Dreamy-Jy/slack/hardware/v1-electronics/Texas Instruments/BQ25186DLHR.stp

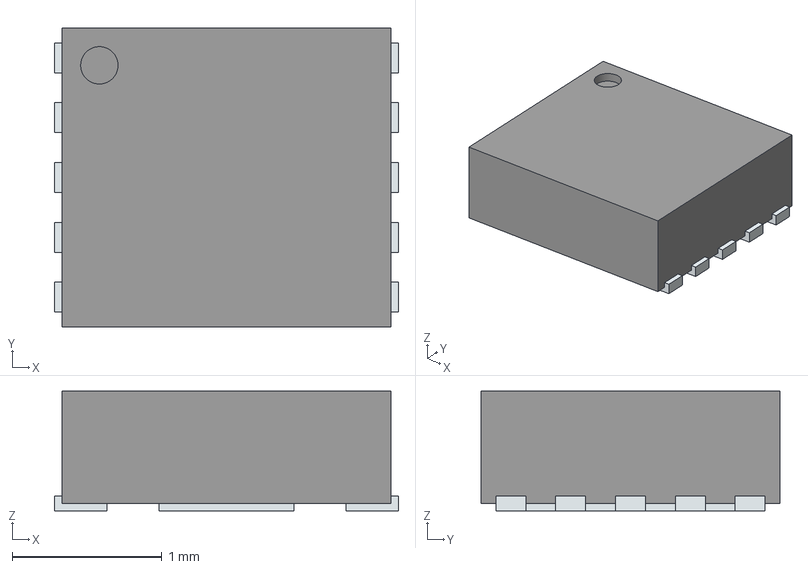
[picture p15: CAD file, 2026-05-10]
hardware/v1-electronics/Texas Instruments/BQ25186DLHR.stp
2.30 x 2.00 x 0.8 mm
ThermalPin
PinsArrayLR
