Dreamy-Jy/slack/hardware/v1-electronics/Texas Instruments/BQ25185DLHR.step

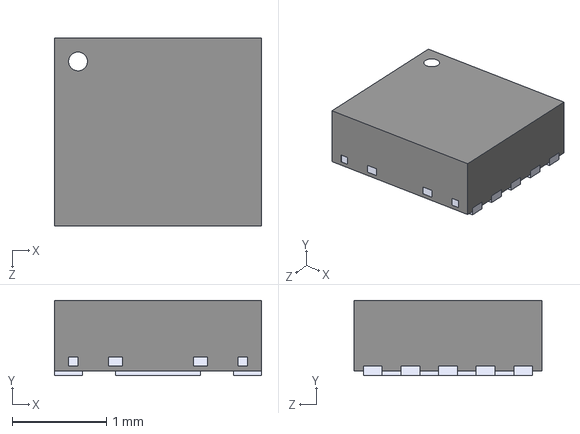
[picture p16: CAD file, 2026-04-30]
hardware/v1-electronics/Texas Instruments/BQ25185DLHR.step
2.20 x 0.8 x 2.00 mm
