Dreamy-Jy/slack/hardware/v1-electronics/controller.kicad_sch

## KiCad design hardware/v1-electronics/controller.kicad_sch (2026-08-18)

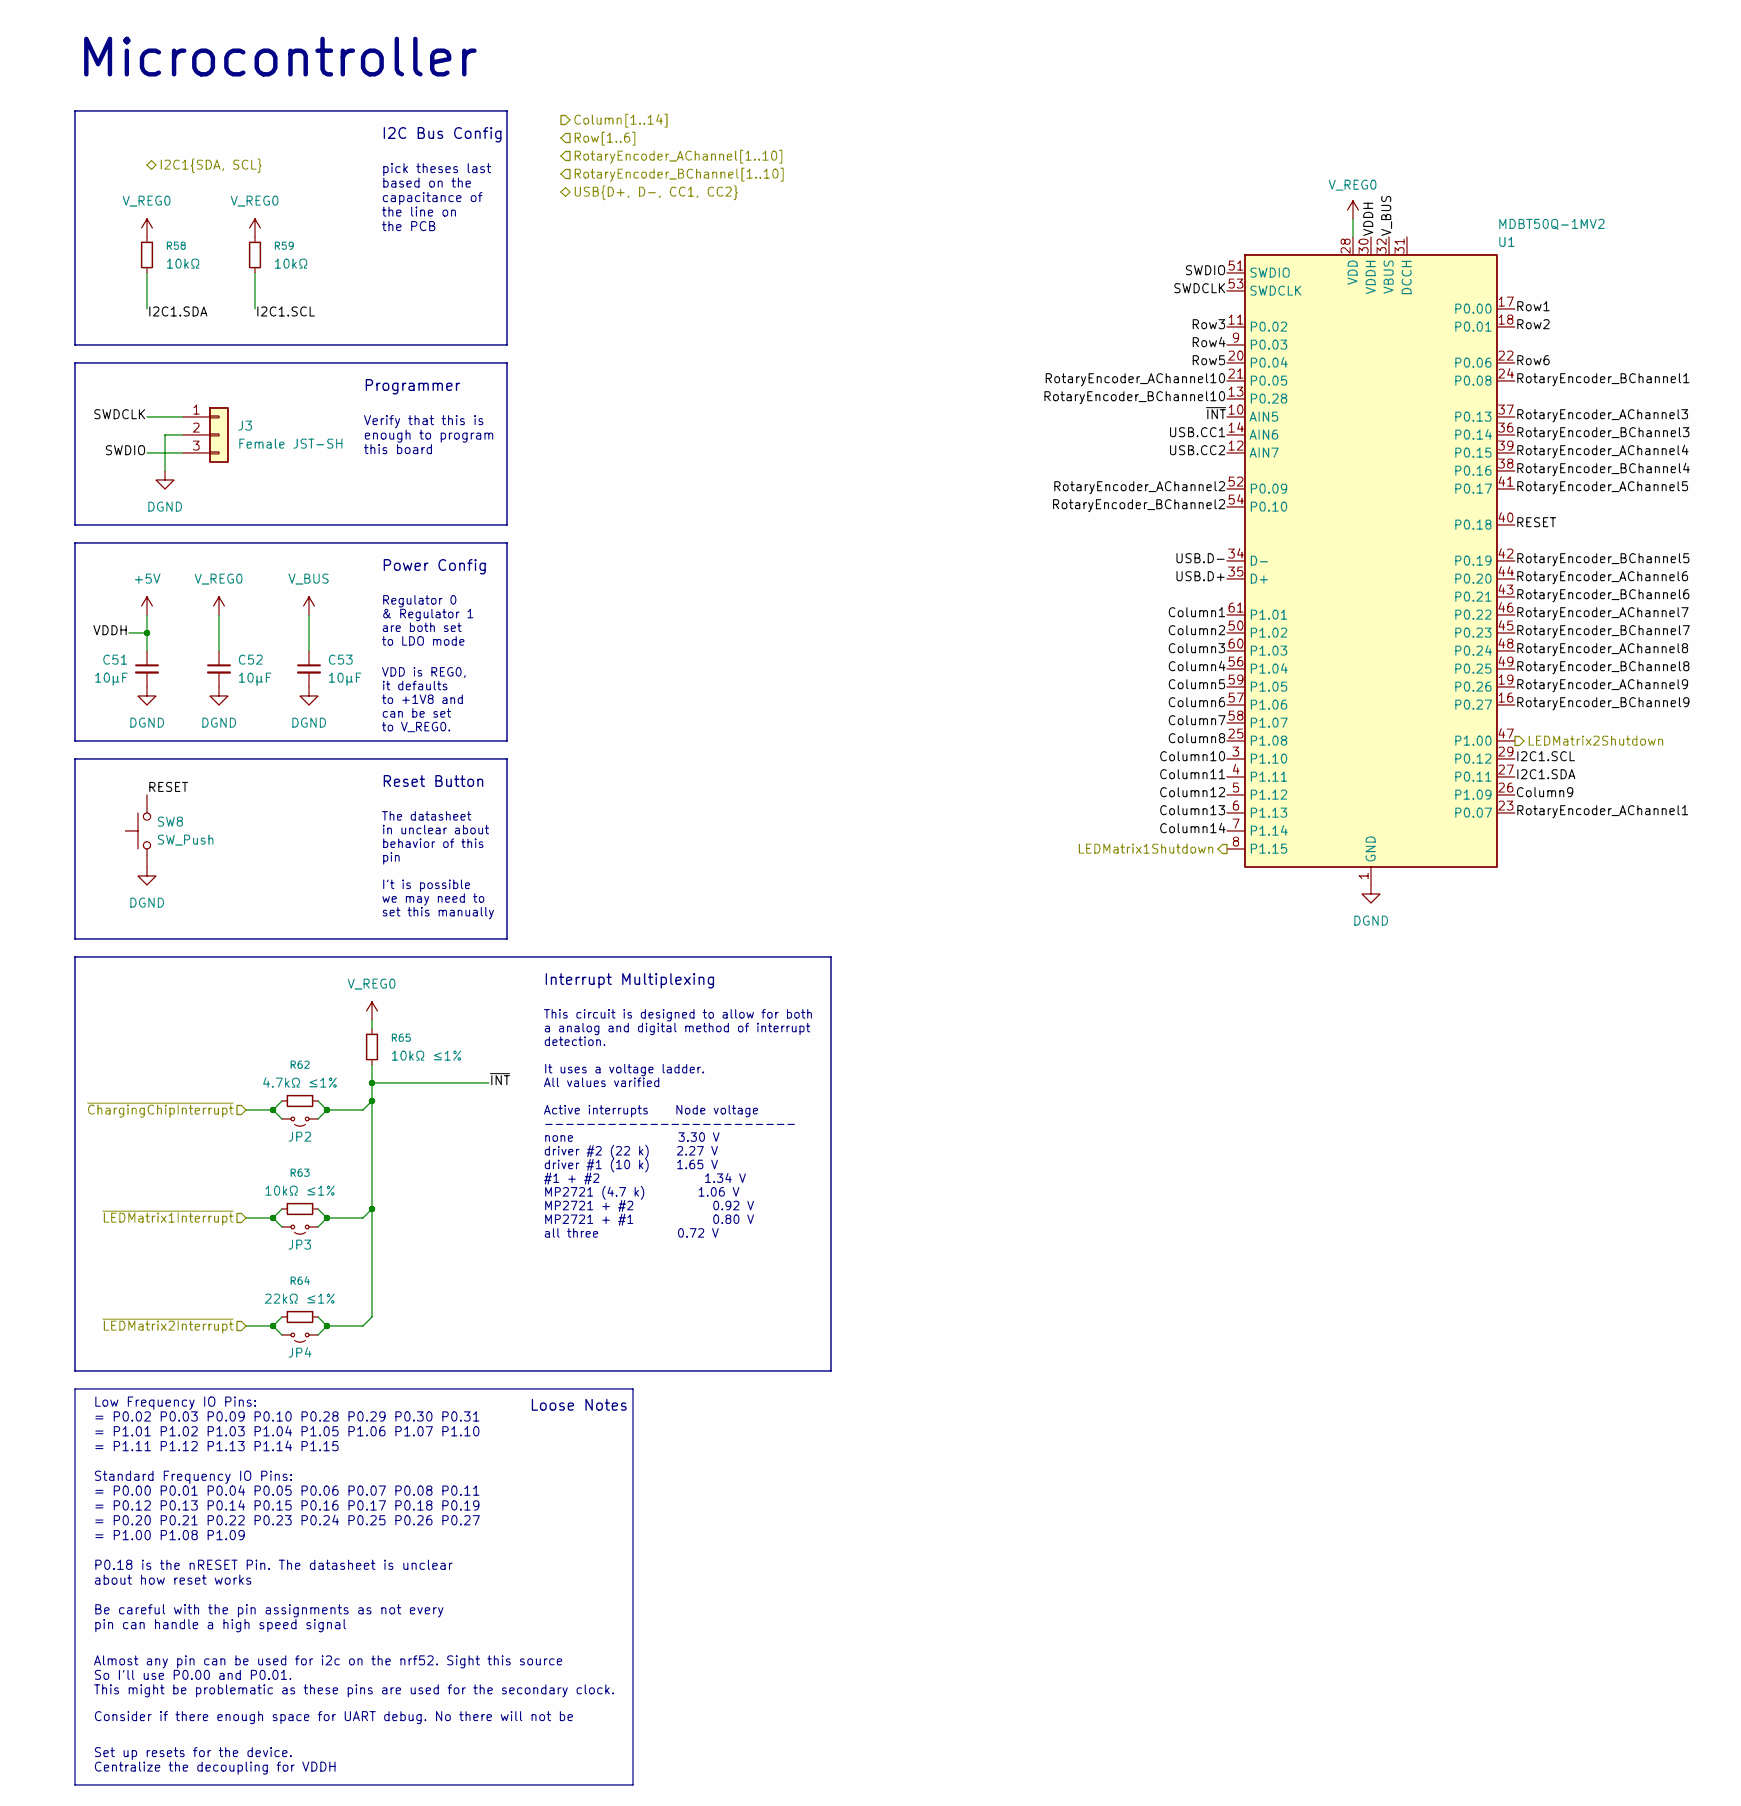
[picture p24: schematic controller.kicad_sch]

Parts:
C51, C52, C53: 10μF; C_0805_2012Metric
J3: Female JST-SH; JST_SH_BM03B-SRSS-TB_1x03-1MP_P1.00mm_Vertical
JP2, JP3, JP4: Jumper_2_Small_Open; PinHeader_1x02_P2.54mm_Vertical
R58, R59: 10kΩ; R_0805_2012Metric
R62: 4.7kΩ ≤1%; R_0805_2012Metric
R63, R65: 10kΩ ≤1%; R_0805_2012Metric
R64: 22kΩ ≤1%; R_0805_2012Metric
SW8: SW_Push; SW_Push_1P1T_XKB_TS-1187A
U1: MDBT50Q-1MV2; Raytac_MDBT50Q

Connections:
+5V: C51.1, U1.30 (VDDH)
Column1: U1.61 (P1.01)
Column2: U1.50 (P1.02)
Column3: U1.60 (P1.03)
Column4: U1.56 (P1.04)
Column5: U1.59 (P1.05)
Column6: U1.57 (P1.06)
Column7: U1.58 (P1.07)
Column8: U1.25 (P1.08)
Column9: U1.26 (P1.09)
Column10: U1.3 (P1.10)
Column11: U1.4 (P1.11)
Column12: U1.5 (P1.12)
Column13: U1.6 (P1.13)
Column14: U1.7 (P1.14)
DGND: C51.2, C52.2, C53.2, J3.2, SW8.1, U1.1 (GND), U1.2 (GND), U1.15 (GND), U1.33 (GND), U1.55 (GND)
I2C1.SCL: R59.2, U1.29 (P0.12)
I2C1.SDA: R58.2, U1.27 (P0.11)
LEDMatrix1Shutdown: U1.8 (P1.15)
LEDMatrix2Shutdown: U1.47 (P1.00)
RESET: SW8.2, U1.40 (P0.18)
RotaryEncoder_AChannel1: U1.23 (P0.07)
RotaryEncoder_AChannel2: U1.52 (P0.09)
RotaryEncoder_AChannel3: U1.37 (P0.13)
RotaryEncoder_AChannel4: U1.39 (P0.15)
RotaryEncoder_AChannel5: U1.41 (P0.17)
RotaryEncoder_AChannel6: U1.44 (P0.20)
RotaryEncoder_AChannel7: U1.46 (P0.22)
RotaryEncoder_AChannel8: U1.48 (P0.24)
RotaryEncoder_AChannel9: U1.19 (P0.26)
RotaryEncoder_AChannel10: U1.21 (P0.05)
RotaryEncoder_BChannel1: U1.24 (P0.08)
RotaryEncoder_BChannel2: U1.54 (P0.10)
RotaryEncoder_BChannel3: U1.36 (P0.14)
RotaryEncoder_BChannel4: U1.38 (P0.16)
RotaryEncoder_BChannel5: U1.42 (P0.19)
RotaryEncoder_BChannel6: U1.43 (P0.21)
RotaryEncoder_BChannel7: U1.45 (P0.23)
RotaryEncoder_BChannel8: U1.49 (P0.25)
RotaryEncoder_BChannel9: U1.16 (P0.27)
RotaryEncoder_BChannel10: U1.13 (P0.28)
Row1: U1.17 (P0.00)
Row2: U1.18 (P0.01)
Row3: U1.11 (P0.02)
Row4: U1.9 (P0.03)
Row5: U1.20 (P0.04)
Row6: U1.22 (P0.06)
SWDCLK: J3.1, U1.53 (SWDCLK)
SWDIO: J3.3, U1.51 (SWDIO)
USB.CC1: U1.14 (P0.30)
USB.CC2: U1.12 (P0.31)
USB.D+: U1.35 (D+)
USB.D-: U1.34 (D-)
V_BUS: C53.1, U1.32 (VBUS)
V_REG0: C52.1, R58.1, R59.1, R65.1, U1.28 (VDD)
~ChargingChipInterrupt: JP2.2 (B), R62.2
~INT: JP2.1 (A), JP3.1 (A), JP4.1 (A), R62.1, R63.1, R64.1, R65.2, U1.10 (P0.29)
~LEDMatrix1Interrupt: JP3.2 (B), R63.2
~LEDMatrix2Interrupt: JP4.2 (B), R64.2

Notes on the sheet:
Loose Notes
Reset Button
Microcontroller
This circuit is designed to allow for both a analog and digital method of interrupt detection. It uses a voltage ladder. All values varified Active interrupts Node voltage ------------------------ none 3.30 V driver #2 (22 k) 2.27 V driver #1 (10 k) 1.65 V #1 + #2 1.34 V MP2721 (4.7 k) 1.06 V MP272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
The datasheet in unclear about behavior of this pin I't is possible we may need to set this manually
Power Config
Interrupt Multiplexing
pick theses last based on the capacitance of the line on the PCB
Low Frequency IO Pins: = P0.02 P0.03 P0.09 P0.10 P0.28 P0.29 P0.30 P0.31 = P1.01 P1.02 P1.03 P1.04 P1.05 P1.06 P1.07 P1.10 = P1.11 P1.12 P1.13 P1.14 P1.15 Standard Frequency IO Pins: = P0.00 P0.01 P0.04 P0.05 P0.06 P0.07 P0.08 P0.11 = P0.12 P0.13 P0.14 P0.15 P0.16 P0.17 P0.18 P0.19 = P0.20 P0.21 P0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
I2C Bus Config
VDD is REG0, it defaults to +1V8 and can be set to V_REG0.
Set up resets for the device. Centralize the decoupling for VDDH
Consider if there enough space for UART debug. No there will not be
Verify that this is enough to program this board
Almost any pin can be used for i2c on the nrf52. Sight this source So I'll use P0.00 and P0.01. This might be problematic as these pins are used for the secondary clock.
Regulator 0 & Regulator 1 are both set to LDO mode
Programmer
