Dreamy-Jy/slack/hardware/v1-electronics/led_matrix.kicad_sch

## KiCad design hardware/v1-electronics/led_matrix.kicad_sch (2026-08-18)

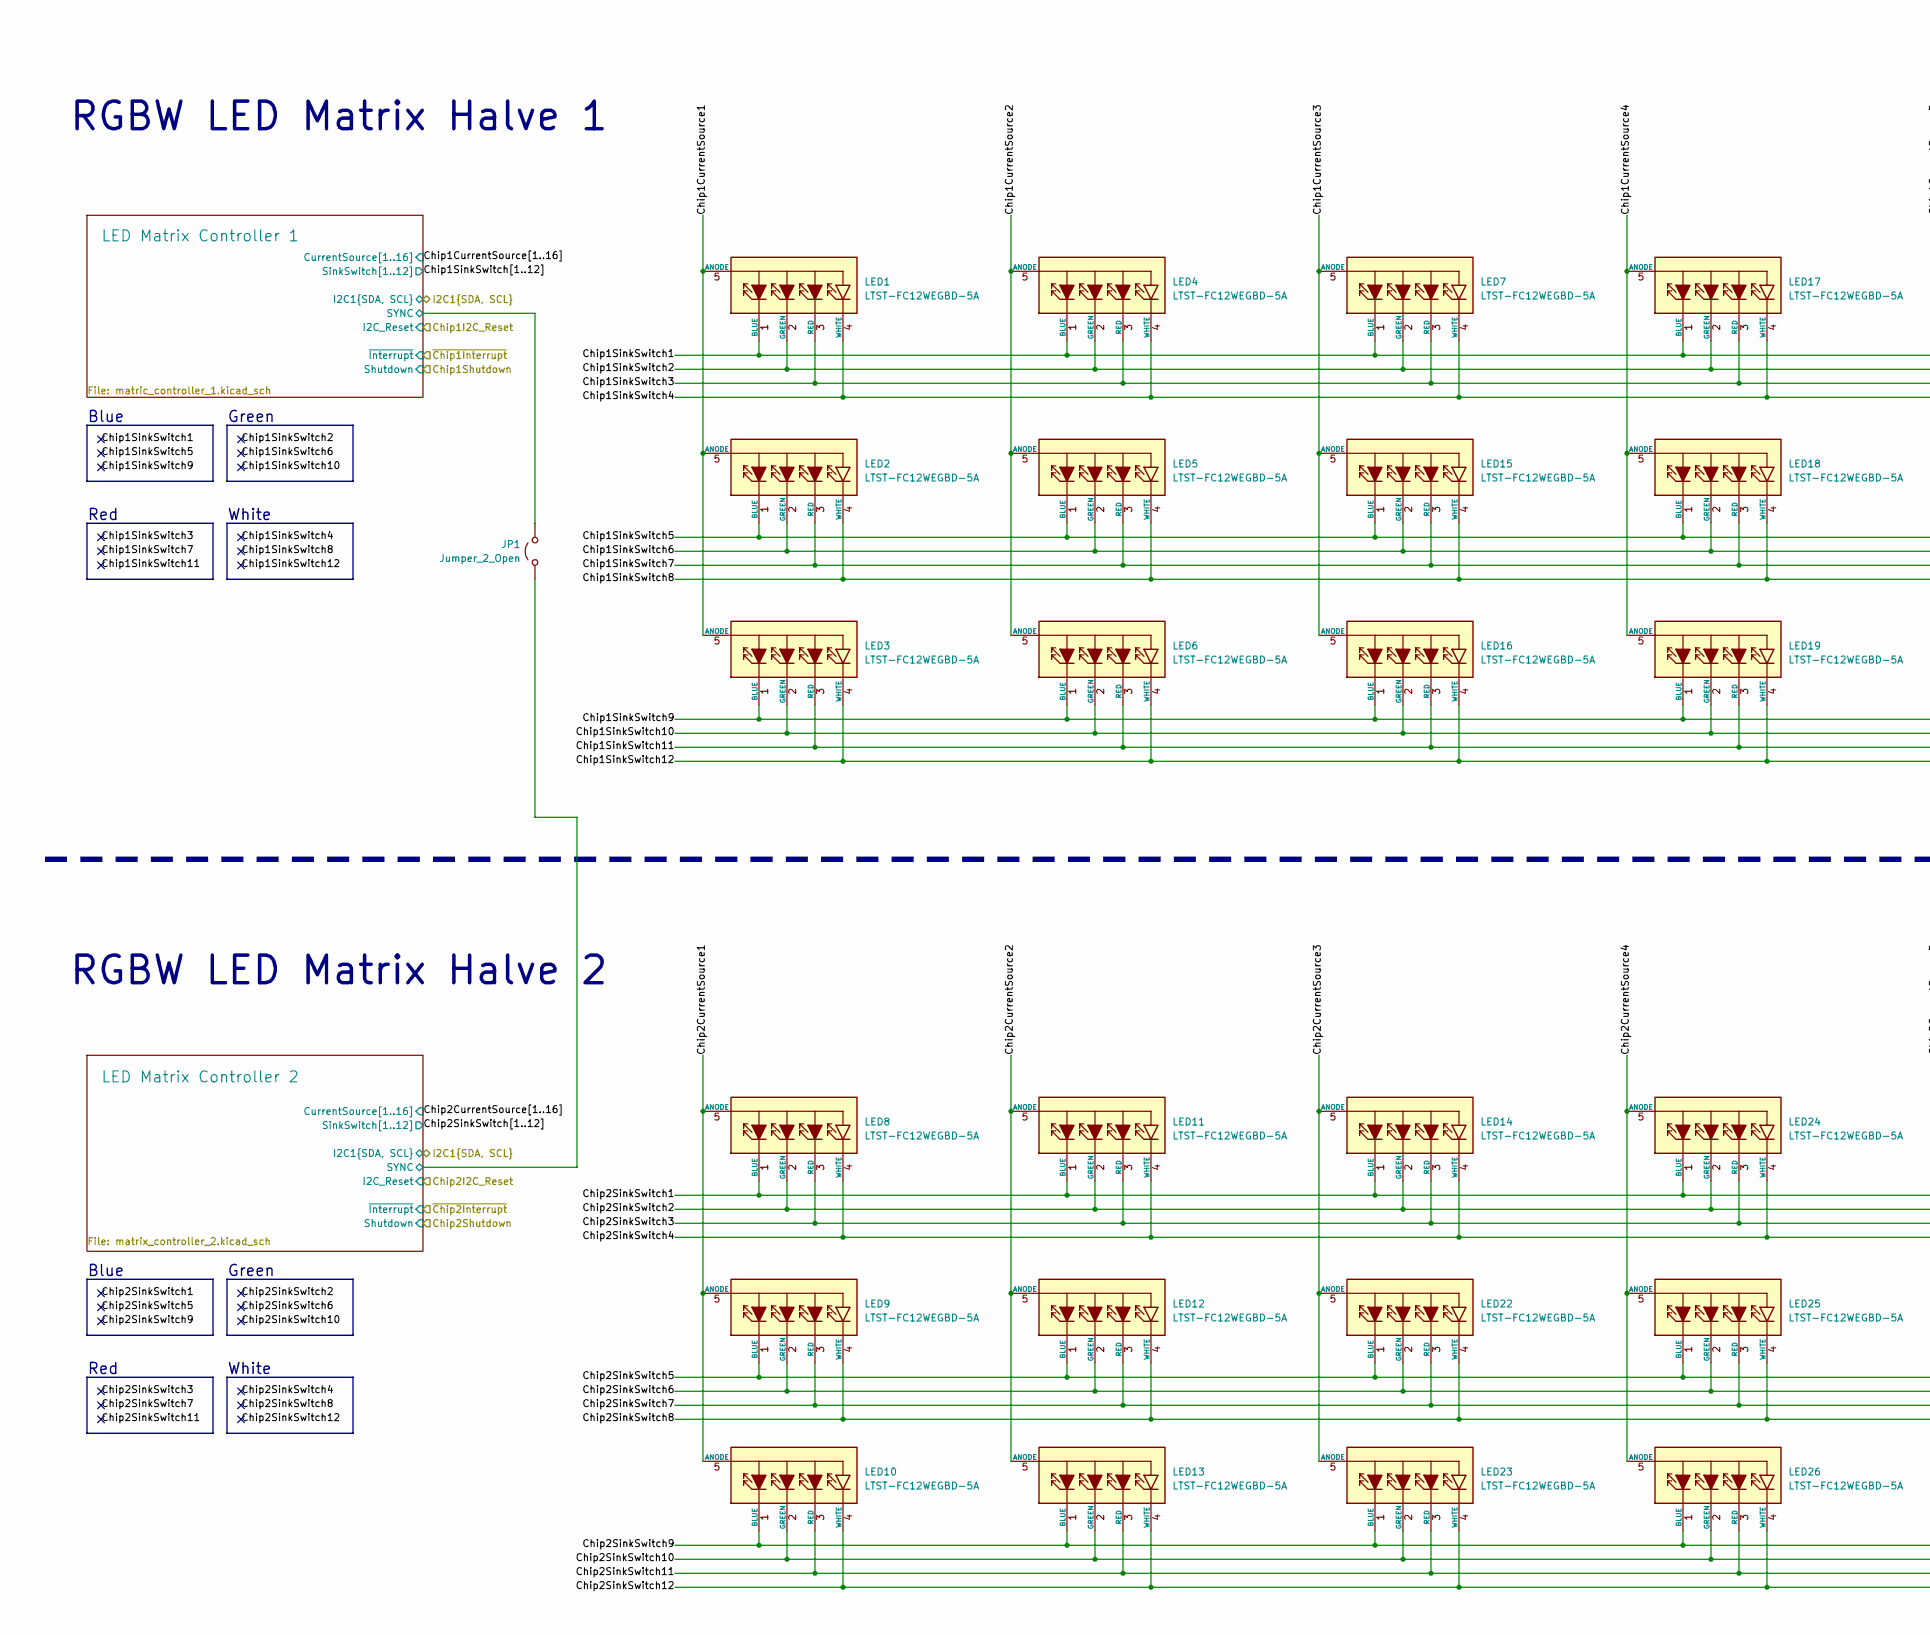
[picture p25: schematic led_matrix.kicad_sch, part in row 1, column 1]

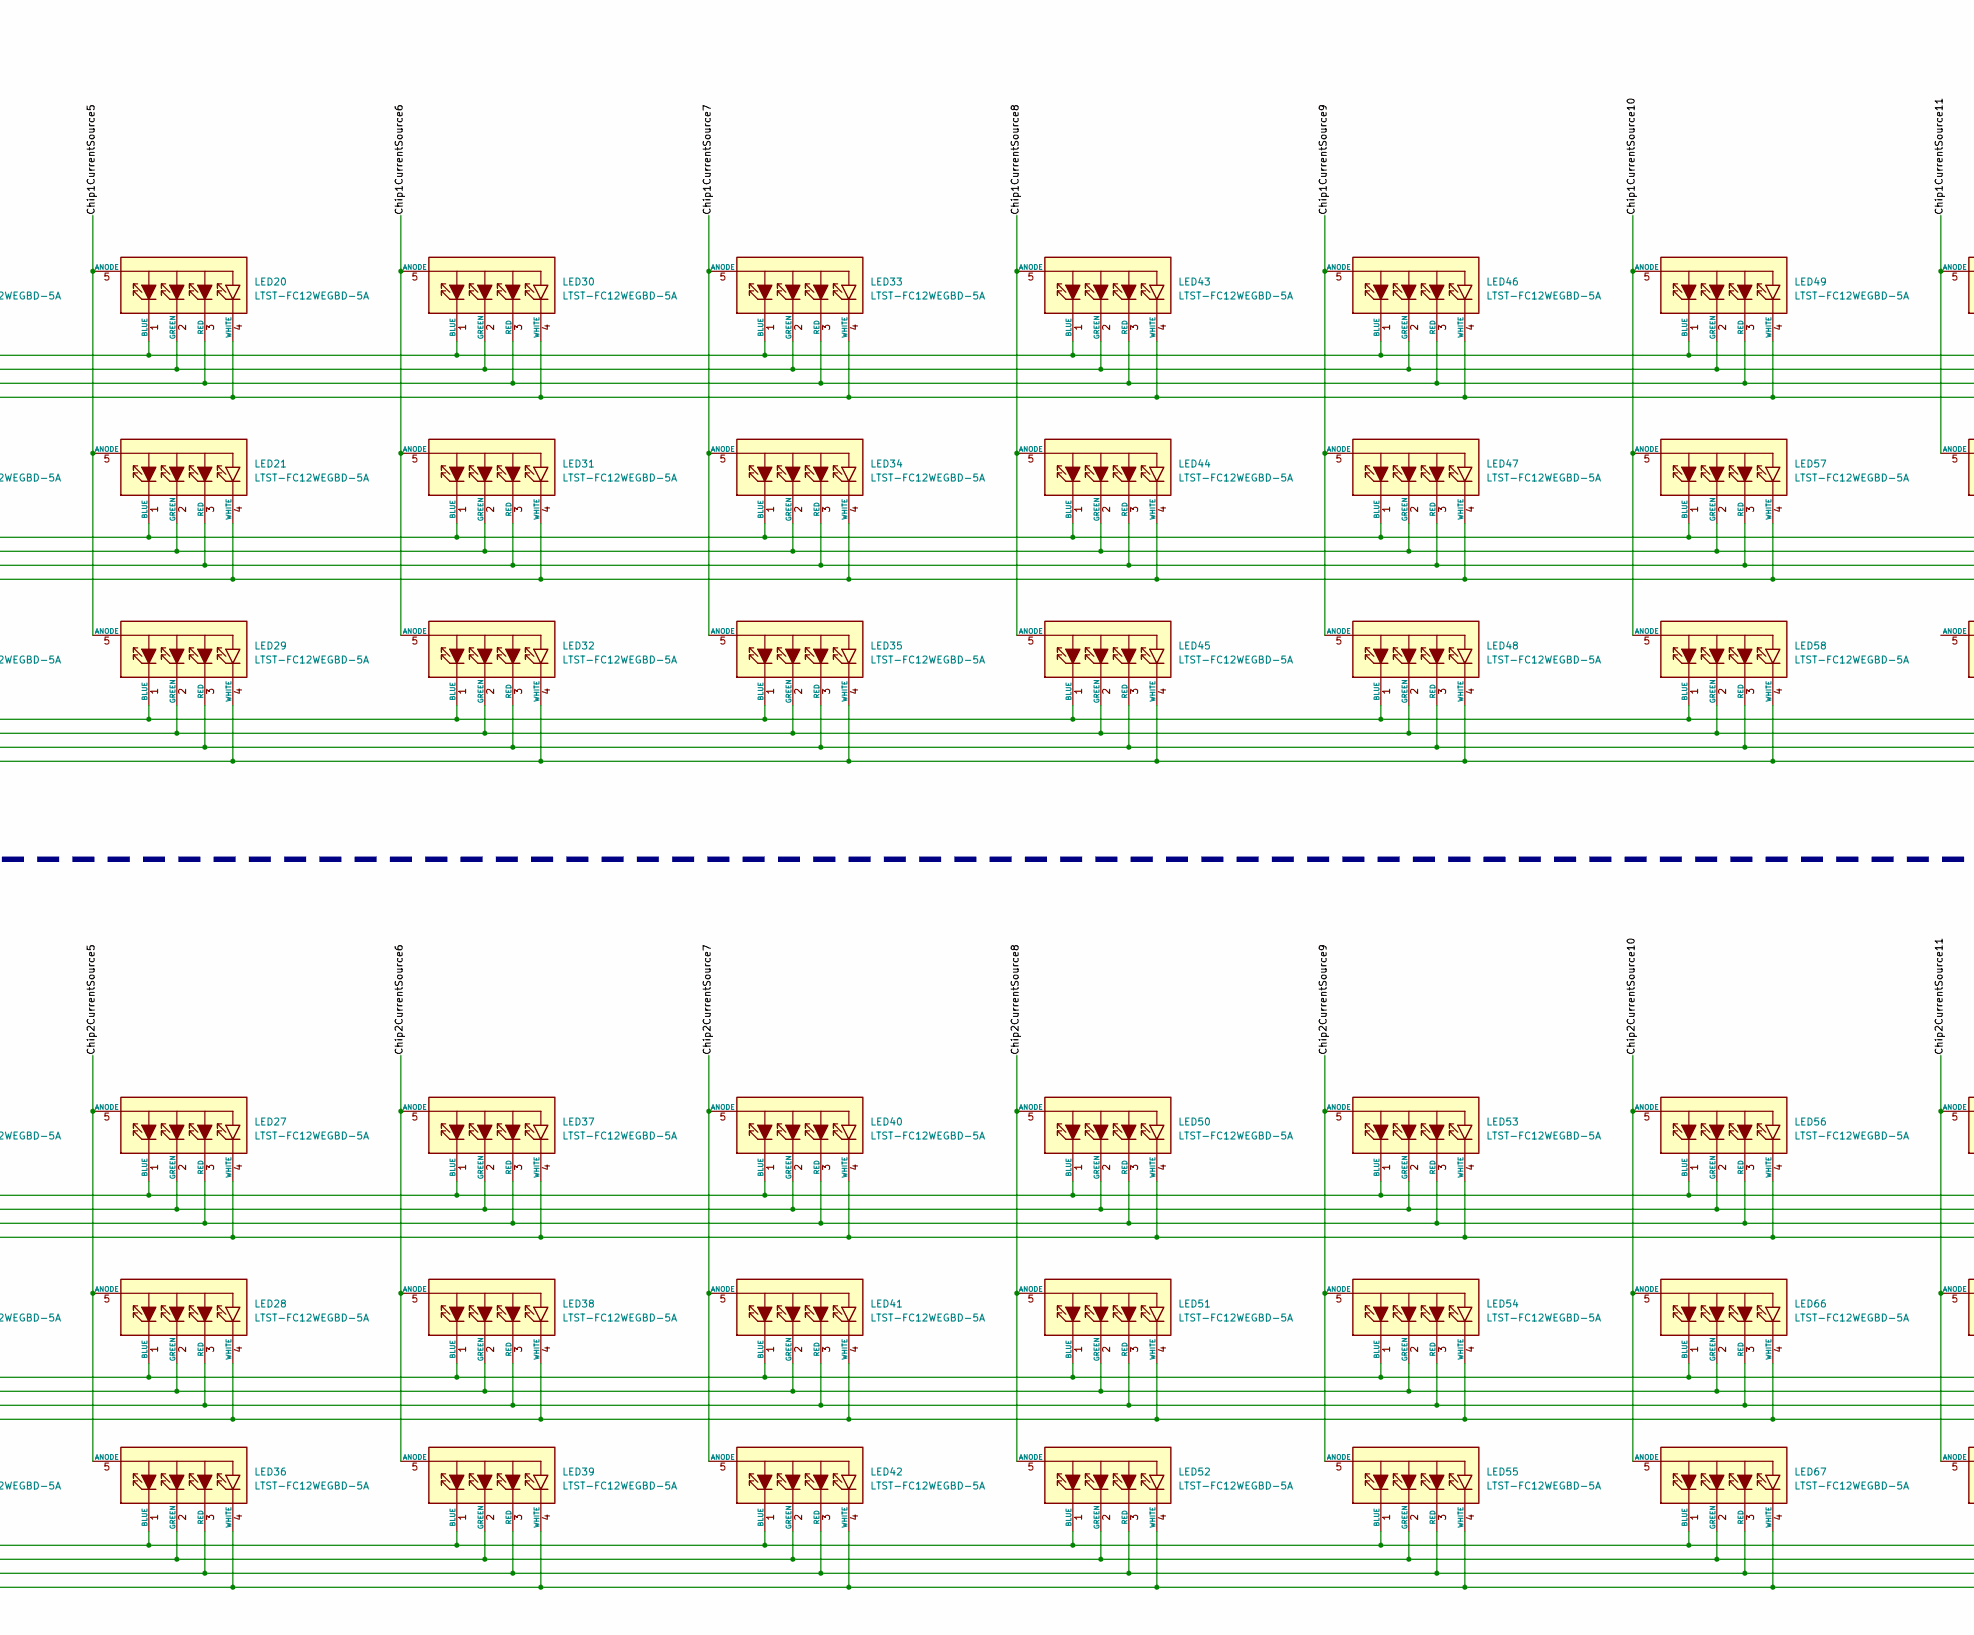
[picture p26: schematic led_matrix.kicad_sch, part in row 1, column 2]

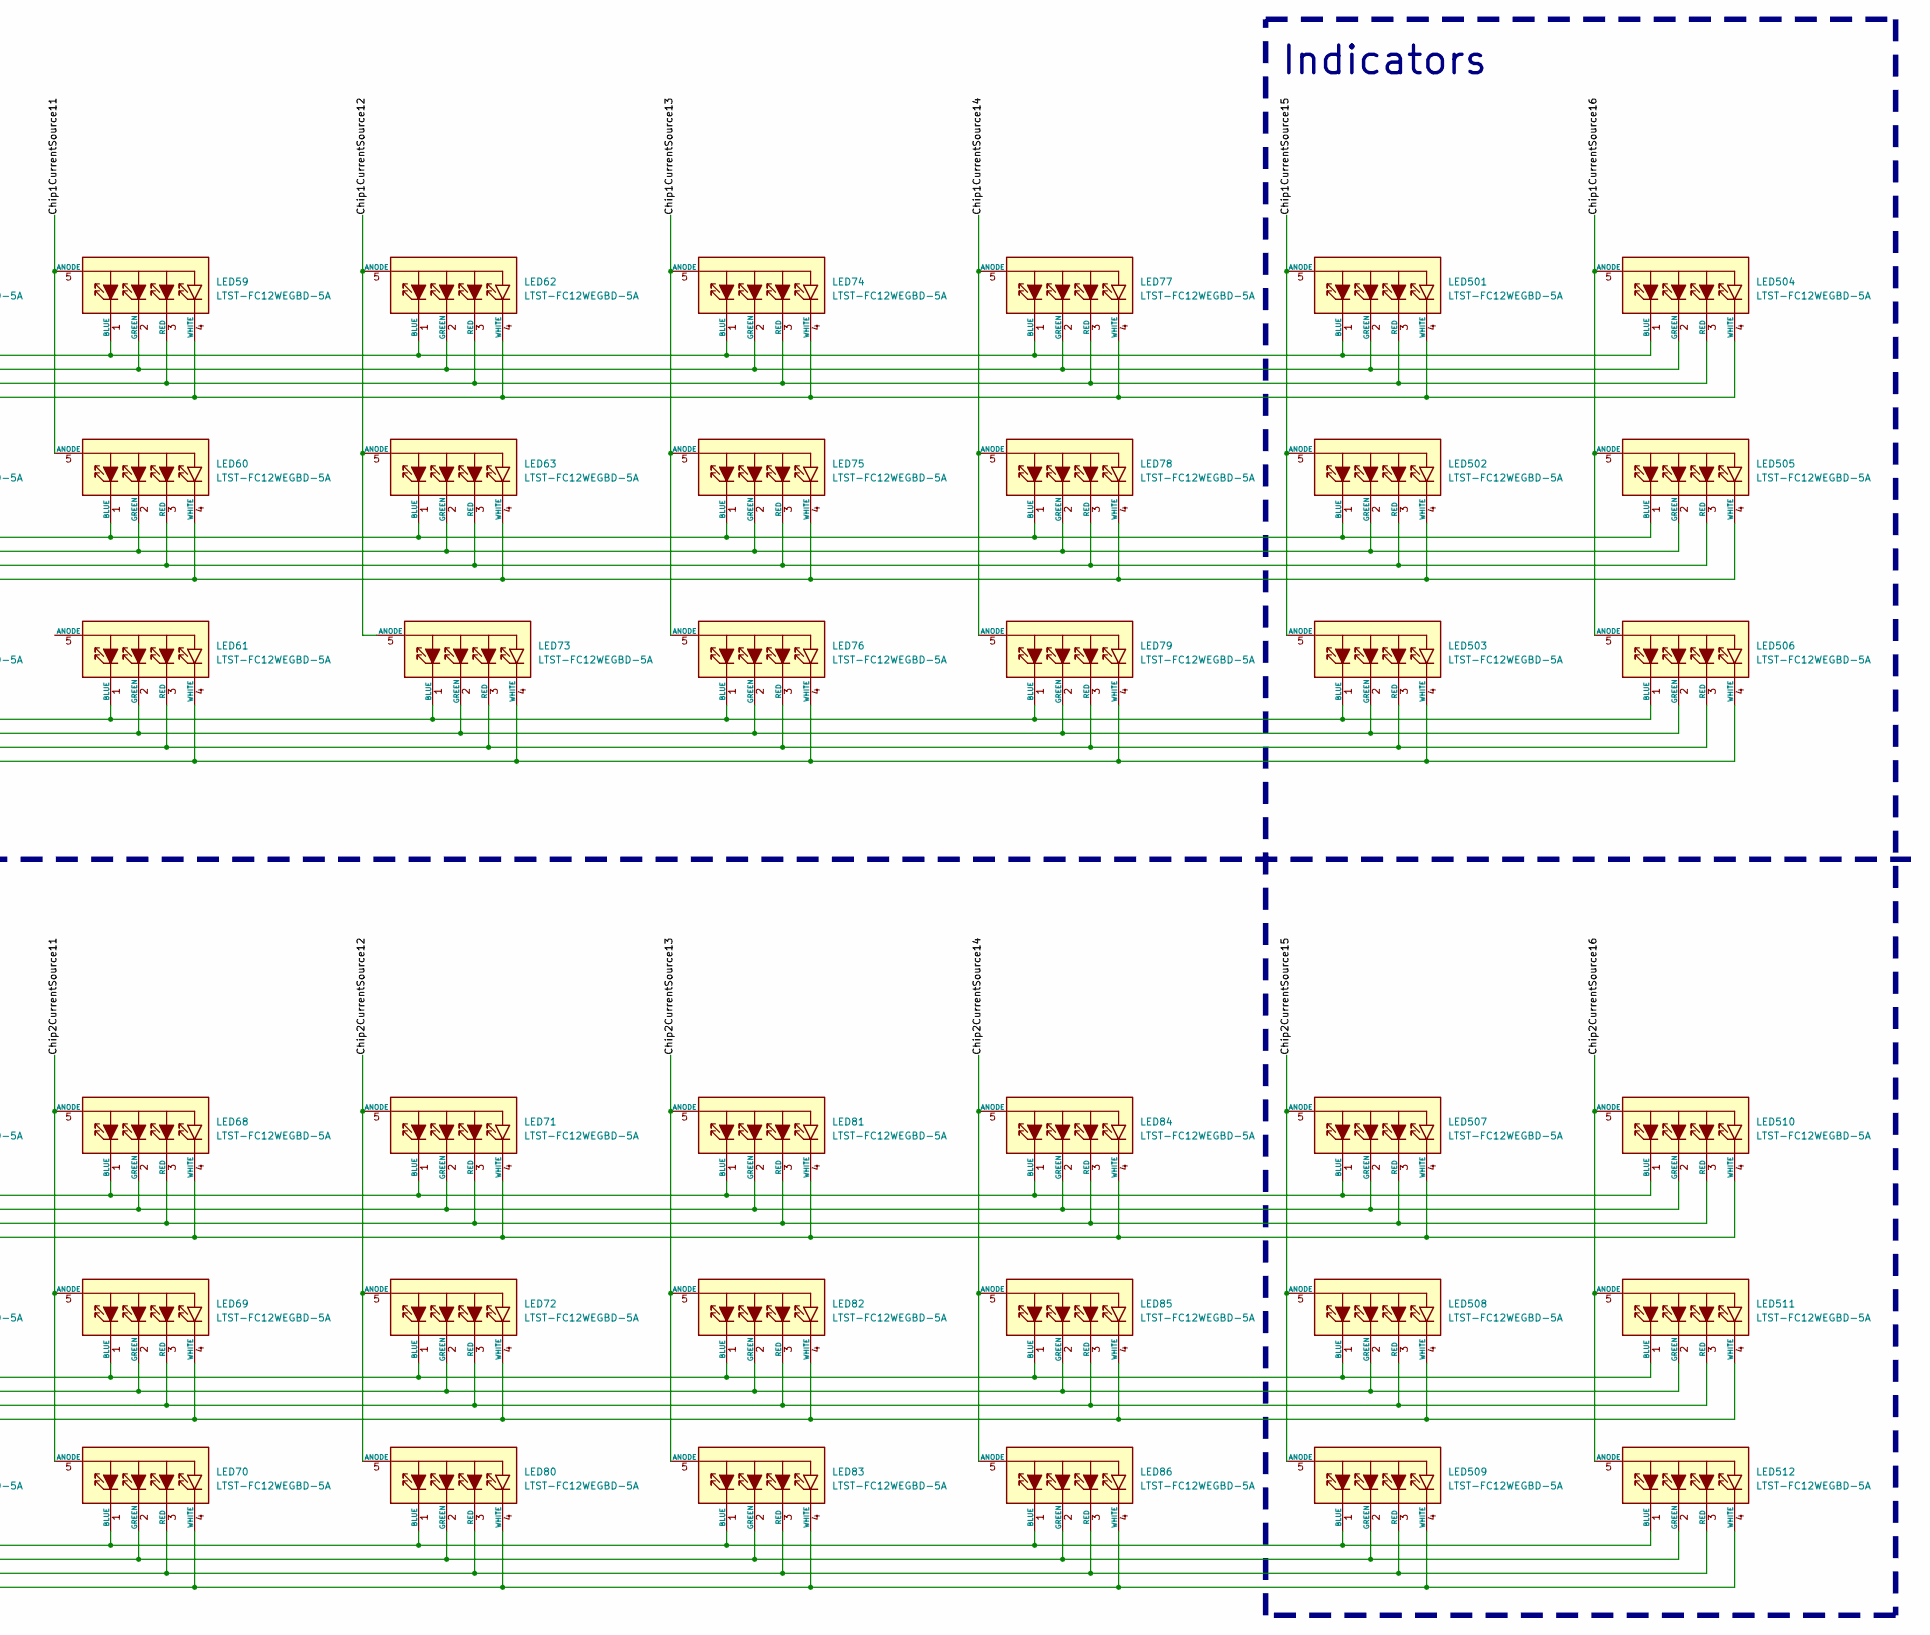
[picture p27: schematic led_matrix.kicad_sch, part in row 1, column 3]

Parts:
JP1: Jumper_2_Open; PinHeader_1x02_P2.54mm_Vertical
LED1, LED2, LED3, LED4, LED5, LED6, LED7, LED8, LED9, LED10, LED11, LED12, LED13, LED14, LED15, LED16, LED17, LED18, LED19, LED20, LED21, LED22, LED23, LED24, LED25, LED26, LED27, LED28, LED29, LED30, LED31, LED32, LED33, LED34, LED35, LED36, LED37, LED38, LED39, LED40, LED41, LED42, LED43, LED44, LED45, LED46, LED47, LED48, LED49, LED50, LED51, LED52, LED53, LED54, LED55, LED56, LED57, LED58, LED59, LED60, LED61, LED62, LED63, LED66, LED67, LED68, LED69, LED70, LED71, LED72, LED73, LED74, LED75, LED76, LED77, LED78, LED79, LED80, LED81, LED82, LED83, LED84, LED85, LED86, LED501, LED502, LED503, LED504, LED505, LED506, LED507, LED508, LED509, LED510, LED511, LED512: LTST-FC12WEGBD-5A; LTSTFC12WEGBD5A; Manufacturer_Part_Number LTST-FC12WEGBD-5A; Mouser Part Number 859-LTST-FC12WEGBD5A

Connections:
Chip1CurrentSource1: LED1.5 (ANODE), LED2.5 (ANODE), LED3.5 (ANODE)
Chip1CurrentSource2: LED4.5 (ANODE), LED5.5 (ANODE), LED6.5 (ANODE)
Chip1CurrentSource3: LED7.5 (ANODE), LED15.5 (ANODE), LED16.5 (ANODE)
Chip1CurrentSource4: LED17.5 (ANODE), LED18.5 (ANODE), LED19.5 (ANODE)
Chip1CurrentSource5: LED20.5 (ANODE), LED21.5 (ANODE), LED29.5 (ANODE)
Chip1CurrentSource6: LED30.5 (ANODE), LED31.5 (ANODE), LED32.5 (ANODE)
Chip1CurrentSource7: LED33.5 (ANODE), LED34.5 (ANODE), LED35.5 (ANODE)
Chip1CurrentSource8: LED43.5 (ANODE), LED44.5 (ANODE), LED45.5 (ANODE)
Chip1CurrentSource9: LED46.5 (ANODE), LED47.5 (ANODE), LED48.5 (ANODE)
Chip1CurrentSource10: LED49.5 (ANODE), LED57.5 (ANODE), LED58.5 (ANODE)
Chip1CurrentSource11: LED59.5 (ANODE), LED60.5 (ANODE)
Chip1CurrentSource12: LED62.5 (ANODE), LED63.5 (ANODE), LED73.5 (ANODE)
Chip1CurrentSource13: LED74.5 (ANODE), LED75.5 (ANODE), LED76.5 (ANODE)
Chip1CurrentSource14: LED77.5 (ANODE), LED78.5 (ANODE), LED79.5 (ANODE)
Chip1CurrentSource15: LED501.5 (ANODE), LED502.5 (ANODE), LED503.5 (ANODE)
Chip1CurrentSource16: LED504.5 (ANODE), LED505.5 (ANODE), LED506.5 (ANODE)
Chip1SinkSwitch1: LED1.1 (BLUE), LED4.1 (BLUE), LED7.1 (BLUE), LED17.1 (BLUE), LED20.1 (BLUE), LED30.1 (BLUE), LED33.1 (BLUE), LED43.1 (BLUE), LED46.1 (BLUE), LED49.1 (BLUE), LED59.1 (BLUE), LED62.1 (BLUE), LED74.1 (BLUE), LED77.1 (BLUE), LED501.1 (BLUE), LED504.1 (BLUE)
Chip1SinkSwitch2: LED1.2 (GREEN), LED4.2 (GREEN), LED7.2 (GREEN), LED17.2 (GREEN), LED20.2 (GREEN), LED30.2 (GREEN), LED33.2 (GREEN), LED43.2 (GREEN), LED46.2 (GREEN), LED49.2 (GREEN), LED59.2 (GREEN), LED62.2 (GREEN), LED74.2 (GREEN), LED77.2 (GREEN), LED501.2 (GREEN), LED504.2 (GREEN)
Chip1SinkSwitch3: LED1.3 (RED), LED4.3 (RED), LED7.3 (RED), LED17.3 (RED), LED20.3 (RED), LED30.3 (RED), LED33.3 (RED), LED43.3 (RED), LED46.3 (RED), LED49.3 (RED), LED59.3 (RED), LED62.3 (RED), LED74.3 (RED), LED77.3 (RED), LED501.3 (RED), LED504.3 (RED)
Chip1SinkSwitch4: LED1.4 (WHITE), LED4.4 (WHITE), LED7.4 (WHITE), LED17.4 (WHITE), LED20.4 (WHITE), LED30.4 (WHITE), LED33.4 (WHITE), LED43.4 (WHITE), LED46.4 (WHITE), LED49.4 (WHITE), LED59.4 (WHITE), LED62.4 (WHITE), LED74.4 (WHITE), LED77.4 (WHITE), LED501.4 (WHITE), LED504.4 (WHITE)
Chip1SinkSwitch5: LED2.1 (BLUE), LED5.1 (BLUE), LED15.1 (BLUE), LED18.1 (BLUE), LED21.1 (BLUE), LED31.1 (BLUE), LED34.1 (BLUE), LED44.1 (BLUE), LED47.1 (BLUE), LED57.1 (BLUE), LED60.1 (BLUE), LED63.1 (BLUE), LED75.1 (BLUE), LED78.1 (BLUE), LED502.1 (BLUE), LED505.1 (BLUE)
Chip1SinkSwitch6: LED2.2 (GREEN), LED5.2 (GREEN), LED15.2 (GREEN), LED18.2 (GREEN), LED21.2 (GREEN), LED31.2 (GREEN), LED34.2 (GREEN), LED44.2 (GREEN), LED47.2 (GREEN), LED57.2 (GREEN), LED60.2 (GREEN), LED63.2 (GREEN), LED75.2 (GREEN), LED78.2 (GREEN), LED502.2 (GREEN), LED505.2 (GREEN)
Chip1SinkSwitch7: LED2.3 (RED), LED5.3 (RED), LED15.3 (RED), LED18.3 (RED), LED21.3 (RED), LED31.3 (RED), LED34.3 (RED), LED44.3 (RED), LED47.3 (RED), LED57.3 (RED), LED60.3 (RED), LED63.3 (RED), LED75.3 (RED), LED78.3 (RED), LED502.3 (RED), LED505.3 (RED)
Chip1SinkSwitch8: LED2.4 (WHITE), LED5.4 (WHITE), LED15.4 (WHITE), LED18.4 (WHITE), LED21.4 (WHITE), LED31.4 (WHITE), LED34.4 (WHITE), LED44.4 (WHITE), LED47.4 (WHITE), LED57.4 (WHITE), LED60.4 (WHITE), LED63.4 (WHITE), LED75.4 (WHITE), LED78.4 (WHITE), LED502.4 (WHITE), LED505.4 (WHITE)
Chip1SinkSwitch9: LED3.1 (BLUE), LED6.1 (BLUE), LED16.1 (BLUE), LED19.1 (BLUE), LED29.1 (BLUE), LED32.1 (BLUE), LED35.1 (BLUE), LED45.1 (BLUE), LED48.1 (BLUE), LED58.1 (BLUE), LED61.1 (BLUE), LED73.1 (BLUE), LED76.1 (BLUE), LED79.1 (BLUE), LED503.1 (BLUE), LED506.1 (BLUE)
Chip1SinkSwitch10: LED3.2 (GREEN), LED6.2 (GREEN), LED16.2 (GREEN), LED19.2 (GREEN), LED29.2 (GREEN), LED32.2 (GREEN), LED35.2 (GREEN), LED45.2 (GREEN), LED48.2 (GREEN), LED58.2 (GREEN), LED61.2 (GREEN), LED73.2 (GREEN), LED76.2 (GREEN), LED79.2 (GREEN), LED503.2 (GREEN), LED506.2 (GREEN)
Chip1SinkSwitch11: LED3.3 (RED), LED6.3 (RED), LED16.3 (RED), LED19.3 (RED), LED29.3 (RED), LED32.3 (RED), LED35.3 (RED), LED45.3 (RED), LED48.3 (RED), LED58.3 (RED), LED61.3 (RED), LED73.3 (RED), LED76.3 (RED), LED79.3 (RED), LED503.3 (RED), LED506.3 (RED)
Chip1SinkSwitch12: LED3.4 (WHITE), LED6.4 (WHITE), LED16.4 (WHITE), LED19.4 (WHITE), LED29.4 (WHITE), LED32.4 (WHITE), LED35.4 (WHITE), LED45.4 (WHITE), LED48.4 (WHITE), LED58.4 (WHITE), LED61.4 (WHITE), LED73.4 (WHITE), LED76.4 (WHITE), LED79.4 (WHITE), LED503.4 (WHITE), LED506.4 (WHITE)
Chip2CurrentSource1: LED8.5 (ANODE), LED9.5 (ANODE), LED10.5 (ANODE)
Chip2CurrentSource2: LED11.5 (ANODE), LED12.5 (ANODE), LED13.5 (ANODE)
Chip2CurrentSource3: LED14.5 (ANODE), LED22.5 (ANODE), LED23.5 (ANODE)
Chip2CurrentSource4: LED24.5 (ANODE), LED25.5 (ANODE), LED26.5 (ANODE)
Chip2CurrentSource5: LED27.5 (ANODE), LED28.5 (ANODE), LED36.5 (ANODE)
Chip2CurrentSource6: LED37.5 (ANODE), LED38.5 (ANODE), LED39.5 (ANODE)
Chip2CurrentSource7: LED40.5 (ANODE), LED41.5 (ANODE), LED42.5 (ANODE)
Chip2CurrentSource8: LED50.5 (ANODE), LED51.5 (ANODE), LED52.5 (ANODE)
Chip2CurrentSource9: LED53.5 (ANODE), LED54.5 (ANODE), LED55.5 (ANODE)
Chip2CurrentSource10: LED56.5 (ANODE), LED66.5 (ANODE), LED67.5 (ANODE)
Chip2CurrentSource11: LED68.5 (ANODE), LED69.5 (ANODE), LED70.5 (ANODE)
Chip2CurrentSource12: LED71.5 (ANODE), LED72.5 (ANODE), LED80.5 (ANODE)
Chip2CurrentSource13: LED81.5 (ANODE), LED82.5 (ANODE), LED83.5 (ANODE)
Chip2CurrentSource14: LED84.5 (ANODE), LED85.5 (ANODE), LED86.5 (ANODE)
Chip2CurrentSource15: LED507.5 (ANODE), LED508.5 (ANODE), LED509.5 (ANODE)
Chip2CurrentSource16: LED510.5 (ANODE), LED511.5 (ANODE), LED512.5 (ANODE)
Chip2SinkSwitch1: LED8.1 (BLUE), LED11.1 (BLUE), LED14.1 (BLUE), LED24.1 (BLUE), LED27.1 (BLUE), LED37.1 (BLUE), LED40.1 (BLUE), LED50.1 (BLUE), LED53.1 (BLUE), LED56.1 (BLUE), LED68.1 (BLUE), LED71.1 (BLUE), LED81.1 (BLUE), LED84.1 (BLUE), LED507.1 (BLUE), LED510.1 (BLUE)
Chip2SinkSwitch2: LED8.2 (GREEN), LED11.2 (GREEN), LED14.2 (GREEN), LED24.2 (GREEN), LED27.2 (GREEN), LED37.2 (GREEN), LED40.2 (GREEN), LED50.2 (GREEN), LED53.2 (GREEN), LED56.2 (GREEN), LED68.2 (GREEN), LED71.2 (GREEN), LED81.2 (GREEN), LED84.2 (GREEN), LED507.2 (GREEN), LED510.2 (GREEN)
Chip2SinkSwitch3: LED8.3 (RED), LED11.3 (RED), LED14.3 (RED), LED24.3 (RED), LED27.3 (RED), LED37.3 (RED), LED40.3 (RED), LED50.3 (RED), LED53.3 (RED), LED56.3 (RED), LED68.3 (RED), LED71.3 (RED), LED81.3 (RED), LED84.3 (RED), LED507.3 (RED), LED510.3 (RED)
Chip2SinkSwitch4: LED8.4 (WHITE), LED11.4 (WHITE), LED14.4 (WHITE), LED24.4 (WHITE), LED27.4 (WHITE), LED37.4 (WHITE), LED40.4 (WHITE), LED50.4 (WHITE), LED53.4 (WHITE), LED56.4 (WHITE), LED68.4 (WHITE), LED71.4 (WHITE), LED81.4 (WHITE), LED84.4 (WHITE), LED507.4 (WHITE), LED510.4 (WHITE)
Chip2SinkSwitch5: LED9.1 (BLUE), LED12.1 (BLUE), LED22.1 (BLUE), LED25.1 (BLUE), LED28.1 (BLUE), LED38.1 (BLUE), LED41.1 (BLUE), LED51.1 (BLUE), LED54.1 (BLUE), LED66.1 (BLUE), LED69.1 (BLUE), LED72.1 (BLUE), LED82.1 (BLUE), LED85.1 (BLUE), LED508.1 (BLUE), LED511.1 (BLUE)
Chip2SinkSwitch6: LED9.2 (GREEN), LED12.2 (GREEN), LED22.2 (GREEN), LED25.2 (GREEN), LED28.2 (GREEN), LED38.2 (GREEN), LED41.2 (GREEN), LED51.2 (GREEN), LED54.2 (GREEN), LED66.2 (GREEN), LED69.2 (GREEN), LED72.2 (GREEN), LED82.2 (GREEN), LED85.2 (GREEN), LED508.2 (GREEN), LED511.2 (GREEN)
Chip2SinkSwitch7: LED9.3 (RED), LED12.3 (RED), LED22.3 (RED), LED25.3 (RED), LED28.3 (RED), LED38.3 (RED), LED41.3 (RED), LED51.3 (RED), LED54.3 (RED), LED66.3 (RED), LED69.3 (RED), LED72.3 (RED), LED82.3 (RED), LED85.3 (RED), LED508.3 (RED), LED511.3 (RED)
Chip2SinkSwitch8: LED9.4 (WHITE), LED12.4 (WHITE), LED22.4 (WHITE), LED25.4 (WHITE), LED28.4 (WHITE), LED38.4 (WHITE), LED41.4 (WHITE), LED51.4 (WHITE), LED54.4 (WHITE), LED66.4 (WHITE), LED69.4 (WHITE), LED72.4 (WHITE), LED82.4 (WHITE), LED85.4 (WHITE), LED508.4 (WHITE), LED511.4 (WHITE)
Chip2SinkSwitch9: LED10.1 (BLUE), LED13.1 (BLUE), LED23.1 (BLUE), LED26.1 (BLUE), LED36.1 (BLUE), LED39.1 (BLUE), LED42.1 (BLUE), LED52.1 (BLUE), LED55.1 (BLUE), LED67.1 (BLUE), LED70.1 (BLUE), LED80.1 (BLUE), LED83.1 (BLUE), LED86.1 (BLUE), LED509.1 (BLUE), LED512.1 (BLUE)
Chip2SinkSwitch10: LED10.2 (GREEN), LED13.2 (GREEN), LED23.2 (GREEN), LED26.2 (GREEN), LED36.2 (GREEN), LED39.2 (GREEN), LED42.2 (GREEN), LED52.2 (GREEN), LED55.2 (GREEN), LED67.2 (GREEN), LED70.2 (GREEN), LED80.2 (GREEN), LED83.2 (GREEN), LED86.2 (GREEN), LED509.2 (GREEN), LED512.2 (GREEN)
Chip2SinkSwitch11: LED10.3 (RED), LED13.3 (RED), LED23.3 (RED), LED26.3 (RED), LED36.3 (RED), LED39.3 (RED), LED42.3 (RED), LED52.3 (RED), LED55.3 (RED), LED67.3 (RED), LED70.3 (RED), LED80.3 (RED), LED83.3 (RED), LED86.3 (RED), LED509.3 (RED), LED512.3 (RED)
Chip2SinkSwitch12: LED10.4 (WHITE), LED13.4 (WHITE), LED23.4 (WHITE), LED26.4 (WHITE), LED36.4 (WHITE), LED39.4 (WHITE), LED42.4 (WHITE), LED52.4 (WHITE), LED55.4 (WHITE), LED67.4 (WHITE), LED70.4 (WHITE), LED80.4 (WHITE), LED83.4 (WHITE), LED86.4 (WHITE), LED509.4 (WHITE), LED512.4 (WHITE)
SYNC: JP1.1 (A), JP1.2 (B)

Notes on the sheet:
Blue
Green
Red
White
Indicators
RGBW LED Matrix Halve 2
RGBW LED Matrix Halve 1
