Dreamy-Jy/slack/hardware/v1-electronics/matric_controller_1.kicad_sch

## KiCad design hardware/v1-electronics/matric_controller_1.kicad_sch (2026-08-18)

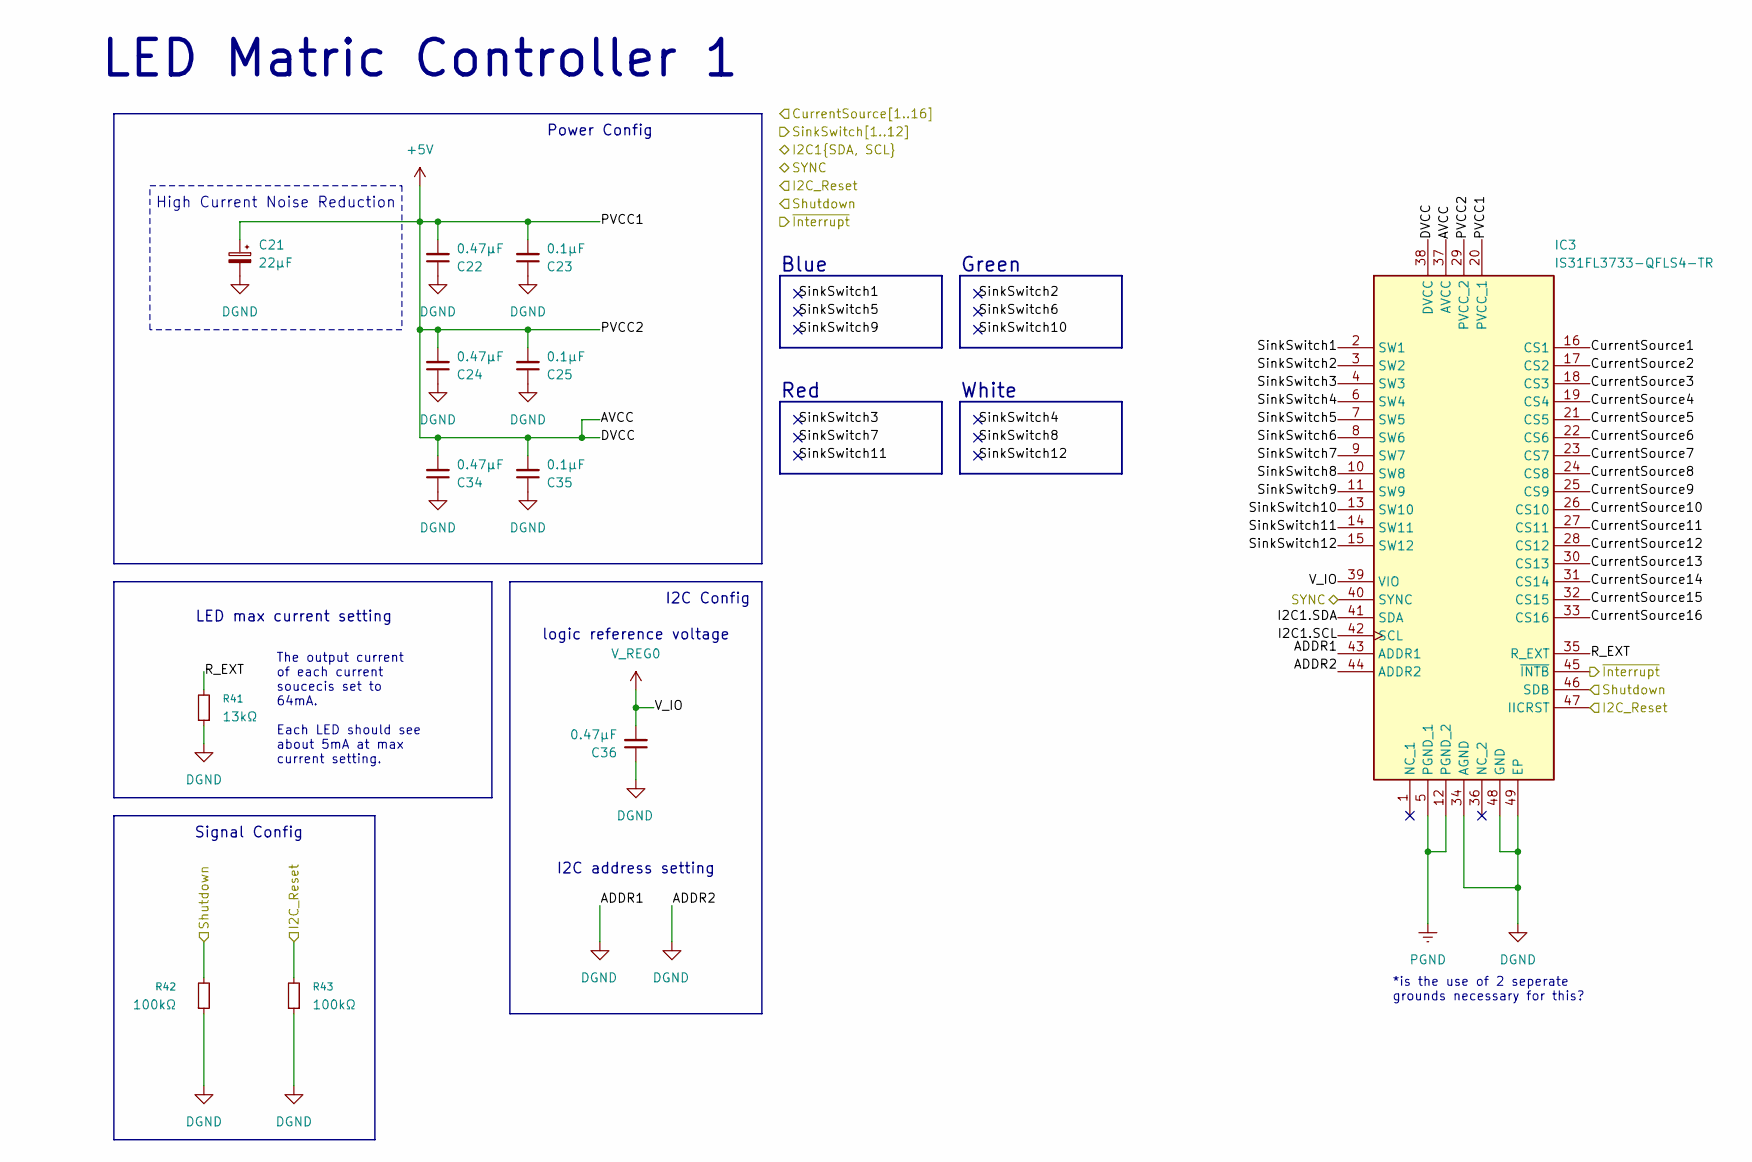
[picture p28: schematic matric_controller_1.kicad_sch]

Parts:
C21: 22μF; CP_EIA-3216-18_Kemet-A
C22, C24, C34, C36: 0.47μF; C_0805_2012Metric
C23, C25, C35: 0.1μF; C_0402_1005Metric
IC3: IS31FL3733-QFLS4-TR; QFN40P600X600X80-49N-D; Manufacturer_Part_Number IS31FL3733-QFLS4-TR; Mouser Part Number 870-31FL3733QFLS4TR
R41: 13kΩ; R_0201_0603Metric
R42, R43: 100kΩ; R_0805_2012Metric

Connections:
+5V: C21.1, C22.2, C23.2, C24.2, C25.2, C34.2, C35.2, IC3.20 (PVCC_1), IC3.29 (PVCC_2), IC3.37 (AVCC), IC3.38 (DVCC)
CurrentSource1: IC3.16 (CS1)
CurrentSource2: IC3.17 (CS2)
CurrentSource3: IC3.18 (CS3)
CurrentSource4: IC3.19 (CS4)
CurrentSource5: IC3.21 (CS5)
CurrentSource6: IC3.22 (CS6)
CurrentSource7: IC3.23 (CS7)
CurrentSource8: IC3.24 (CS8)
CurrentSource9: IC3.25 (CS9)
CurrentSource10: IC3.26 (CS10)
CurrentSource11: IC3.27 (CS11)
CurrentSource12: IC3.28 (CS12)
CurrentSource13: IC3.30 (CS13)
CurrentSource14: IC3.31 (CS14)
CurrentSource15: IC3.32 (CS15)
CurrentSource16: IC3.33 (CS16)
DGND: C21.2, C22.1, C23.1, C24.1, C25.1, C34.1, C35.1, C36.1, IC3.34 (AGND), IC3.43 (ADDR1), IC3.44 (ADDR2), IC3.48 (GND), IC3.49 (EP), R41.1, R42.1, R43.1
I2C1.SCL: IC3.42 (SCL)
I2C1.SDA: IC3.41 (SDA)
I2C_Reset: IC3.47 (IICRST), R43.2
PGND: IC3.5 (PGND_1), IC3.12 (PGND_2)
R_EXT: IC3.35 (R_EXT), R41.2
SYNC: IC3.40 (SYNC)
Shutdown: IC3.46 (SDB), R42.2
SinkSwitch1: IC3.2 (SW1)
SinkSwitch2: IC3.3 (SW2)
SinkSwitch3: IC3.4 (SW3)
SinkSwitch4: IC3.6 (SW4)
SinkSwitch5: IC3.7 (SW5)
SinkSwitch6: IC3.8 (SW6)
SinkSwitch7: IC3.9 (SW7)
SinkSwitch8: IC3.10 (SW8)
SinkSwitch9: IC3.11 (SW9)
SinkSwitch10: IC3.13 (SW10)
SinkSwitch11: IC3.14 (SW11)
SinkSwitch12: IC3.15 (SW12)
V_REG0: C36.2, IC3.39 (VIO)
~Interrupt: IC3.45 (~INTB)

Notes on the sheet:
The output current of each current soucecis set to 64mA. Each LED should see about 5mA at max current setting.
Blue
I2C address setting
White
Green
Signal Config
*is the use of 2 seperate grounds necessary for this?
LED Matric Controller 1
logic reference voltage
LED max current setting
Red
I2C Config
Power Config
High Current Noise Reduction
