Dreamy-Jy/slack/hardware/v1-electronics/matrix_controller_2.kicad_sch

## KiCad design hardware/v1-electronics/matrix_controller_2.kicad_sch (2026-08-18)

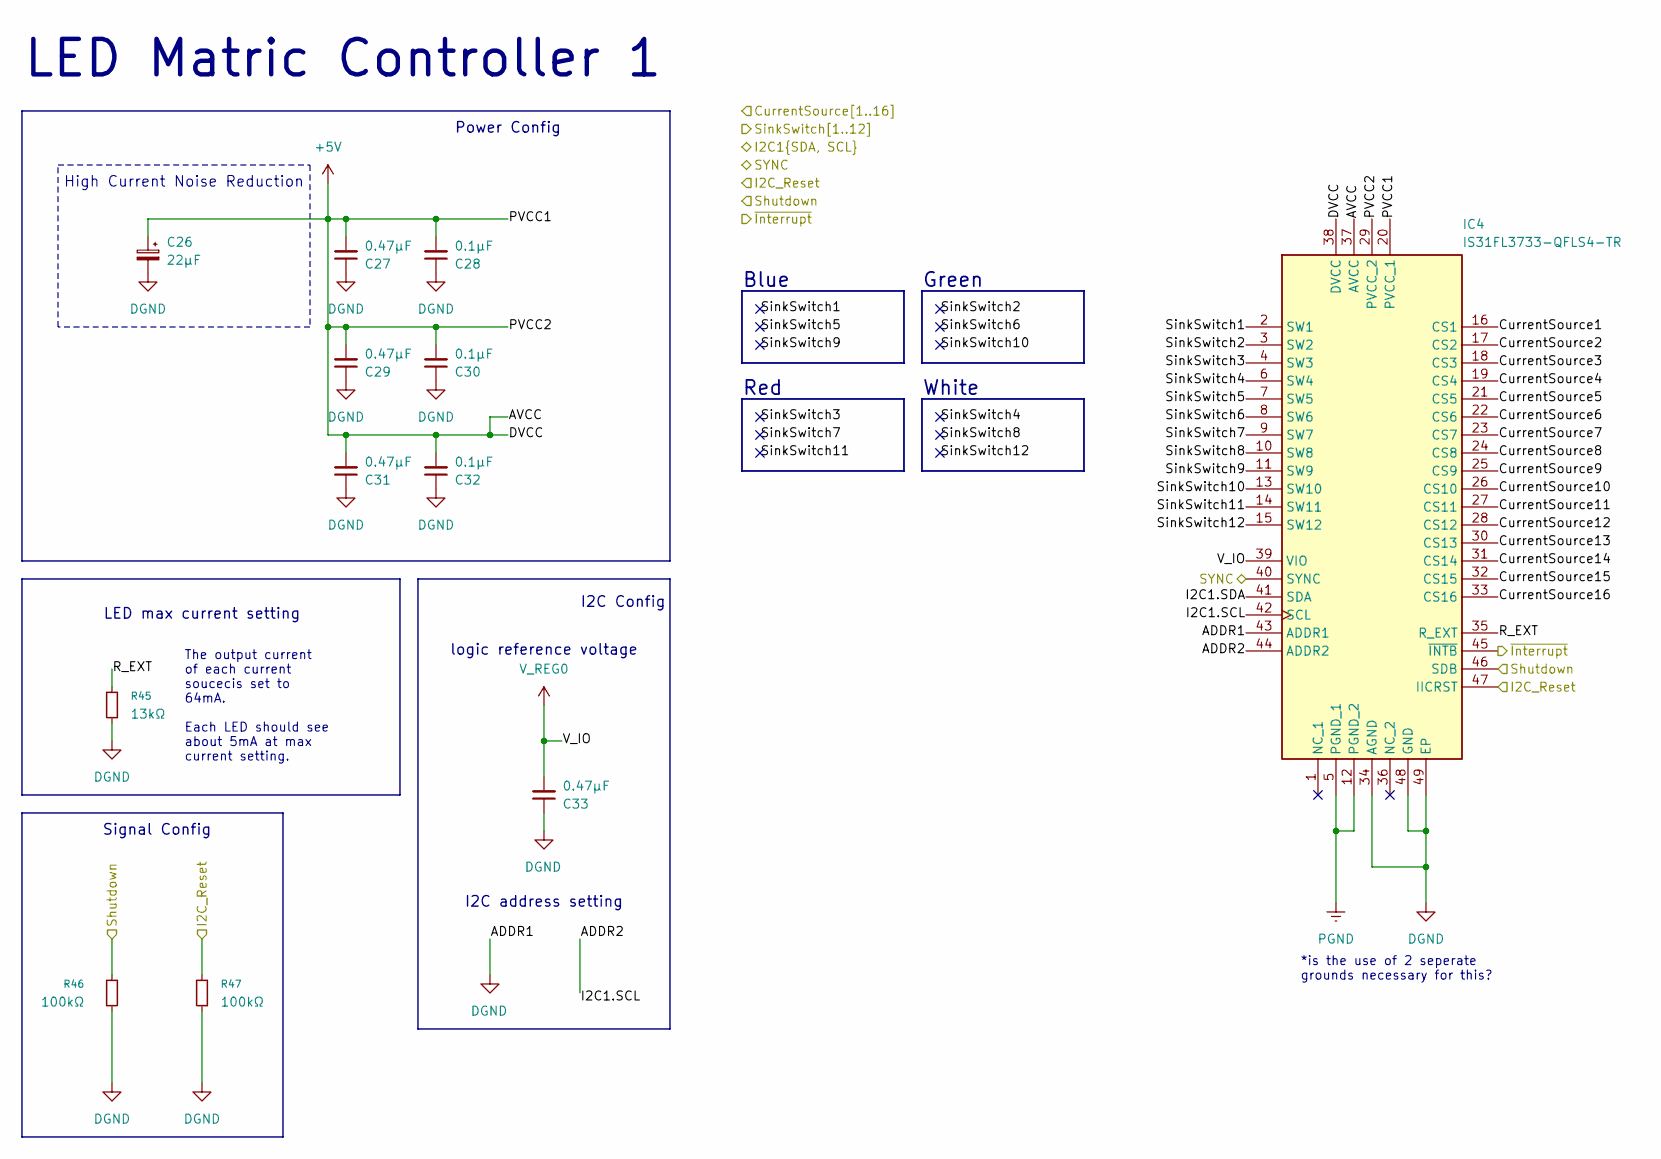
[picture p29: schematic matrix_controller_2.kicad_sch]

Parts:
C26: 22μF; CP_EIA-3216-18_Kemet-A
C27, C29, C31, C33: 0.47μF; C_0805_2012Metric
C28, C30, C32: 0.1μF; C_0402_1005Metric
IC4: IS31FL3733-QFLS4-TR; QFN40P600X600X80-49N-D; Manufacturer_Part_Number IS31FL3733-QFLS4-TR; Mouser Part Number 870-31FL3733QFLS4TR
R45: 13kΩ; R_0201_0603Metric
R46, R47: 100kΩ; R_0805_2012Metric

Connections:
+5V: C26.1, C27.2, C28.2, C29.2, C30.2, C31.2, C32.2, IC4.20 (PVCC_1), IC4.29 (PVCC_2), IC4.37 (AVCC), IC4.38 (DVCC)
ADDR2: IC4.42 (SCL), IC4.44 (ADDR2)
CurrentSource1: IC4.16 (CS1)
CurrentSource2: IC4.17 (CS2)
CurrentSource3: IC4.18 (CS3)
CurrentSource4: IC4.19 (CS4)
CurrentSource5: IC4.21 (CS5)
CurrentSource6: IC4.22 (CS6)
CurrentSource7: IC4.23 (CS7)
CurrentSource8: IC4.24 (CS8)
CurrentSource9: IC4.25 (CS9)
CurrentSource10: IC4.26 (CS10)
CurrentSource11: IC4.27 (CS11)
CurrentSource12: IC4.28 (CS12)
CurrentSource13: IC4.30 (CS13)
CurrentSource14: IC4.31 (CS14)
CurrentSource15: IC4.32 (CS15)
CurrentSource16: IC4.33 (CS16)
DGND: C26.2, C27.1, C28.1, C29.1, C30.1, C31.1, C32.1, C33.1, IC4.34 (AGND), IC4.43 (ADDR1), IC4.48 (GND), IC4.49 (EP), R45.1, R46.1, R47.1
I2C1.SDA: IC4.41 (SDA)
I2C_Reset: IC4.47 (IICRST), R47.2
PGND: IC4.5 (PGND_1), IC4.12 (PGND_2)
R_EXT: IC4.35 (R_EXT), R45.2
SYNC: IC4.40 (SYNC)
Shutdown: IC4.46 (SDB), R46.2
SinkSwitch1: IC4.2 (SW1)
SinkSwitch2: IC4.3 (SW2)
SinkSwitch3: IC4.4 (SW3)
SinkSwitch4: IC4.6 (SW4)
SinkSwitch5: IC4.7 (SW5)
SinkSwitch6: IC4.8 (SW6)
SinkSwitch7: IC4.9 (SW7)
SinkSwitch8: IC4.10 (SW8)
SinkSwitch9: IC4.11 (SW9)
SinkSwitch10: IC4.13 (SW10)
SinkSwitch11: IC4.14 (SW11)
SinkSwitch12: IC4.15 (SW12)
V_REG0: C33.2, IC4.39 (VIO)
~Interrupt: IC4.45 (~INTB)

Notes on the sheet:
The output current of each current soucecis set to 64mA. Each LED should see about 5mA at max current setting.
High Current Noise Reduction
I2C Config
Red
LED Matric Controller 1
Signal Config
Blue
I2C address setting
LED max current setting
White
*is the use of 2 seperate grounds necessary for this?
logic reference voltage
Green
Power Config
