Dreamy-Jy/slack/hardware/v1-electronics/power.kicad_sch

## KiCad design hardware/v1-electronics/power.kicad_sch (2026-08-18)

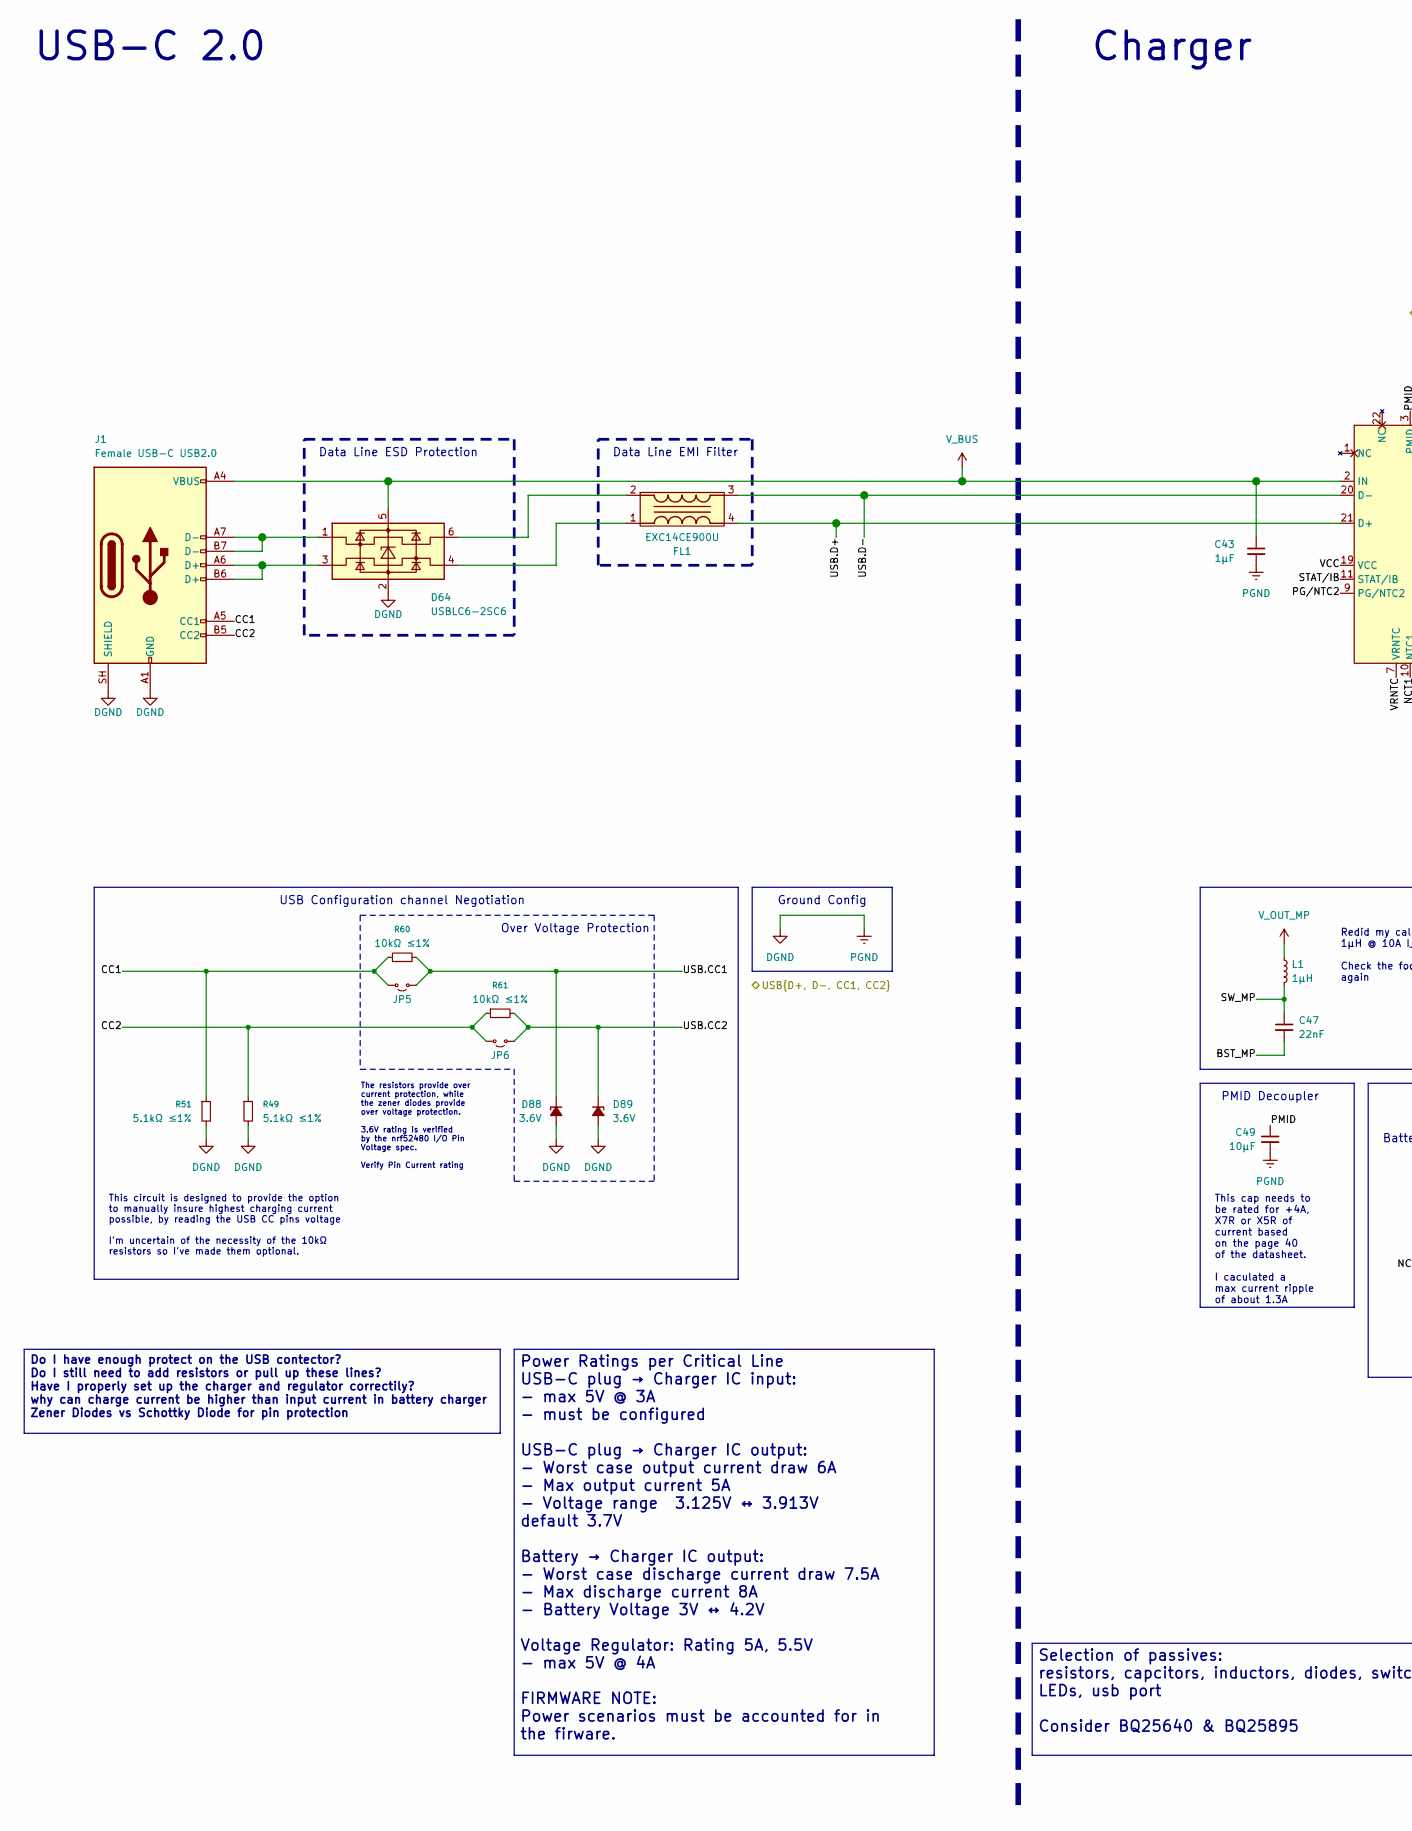
[picture p30: schematic power.kicad_sch, part in row 1, column 1]

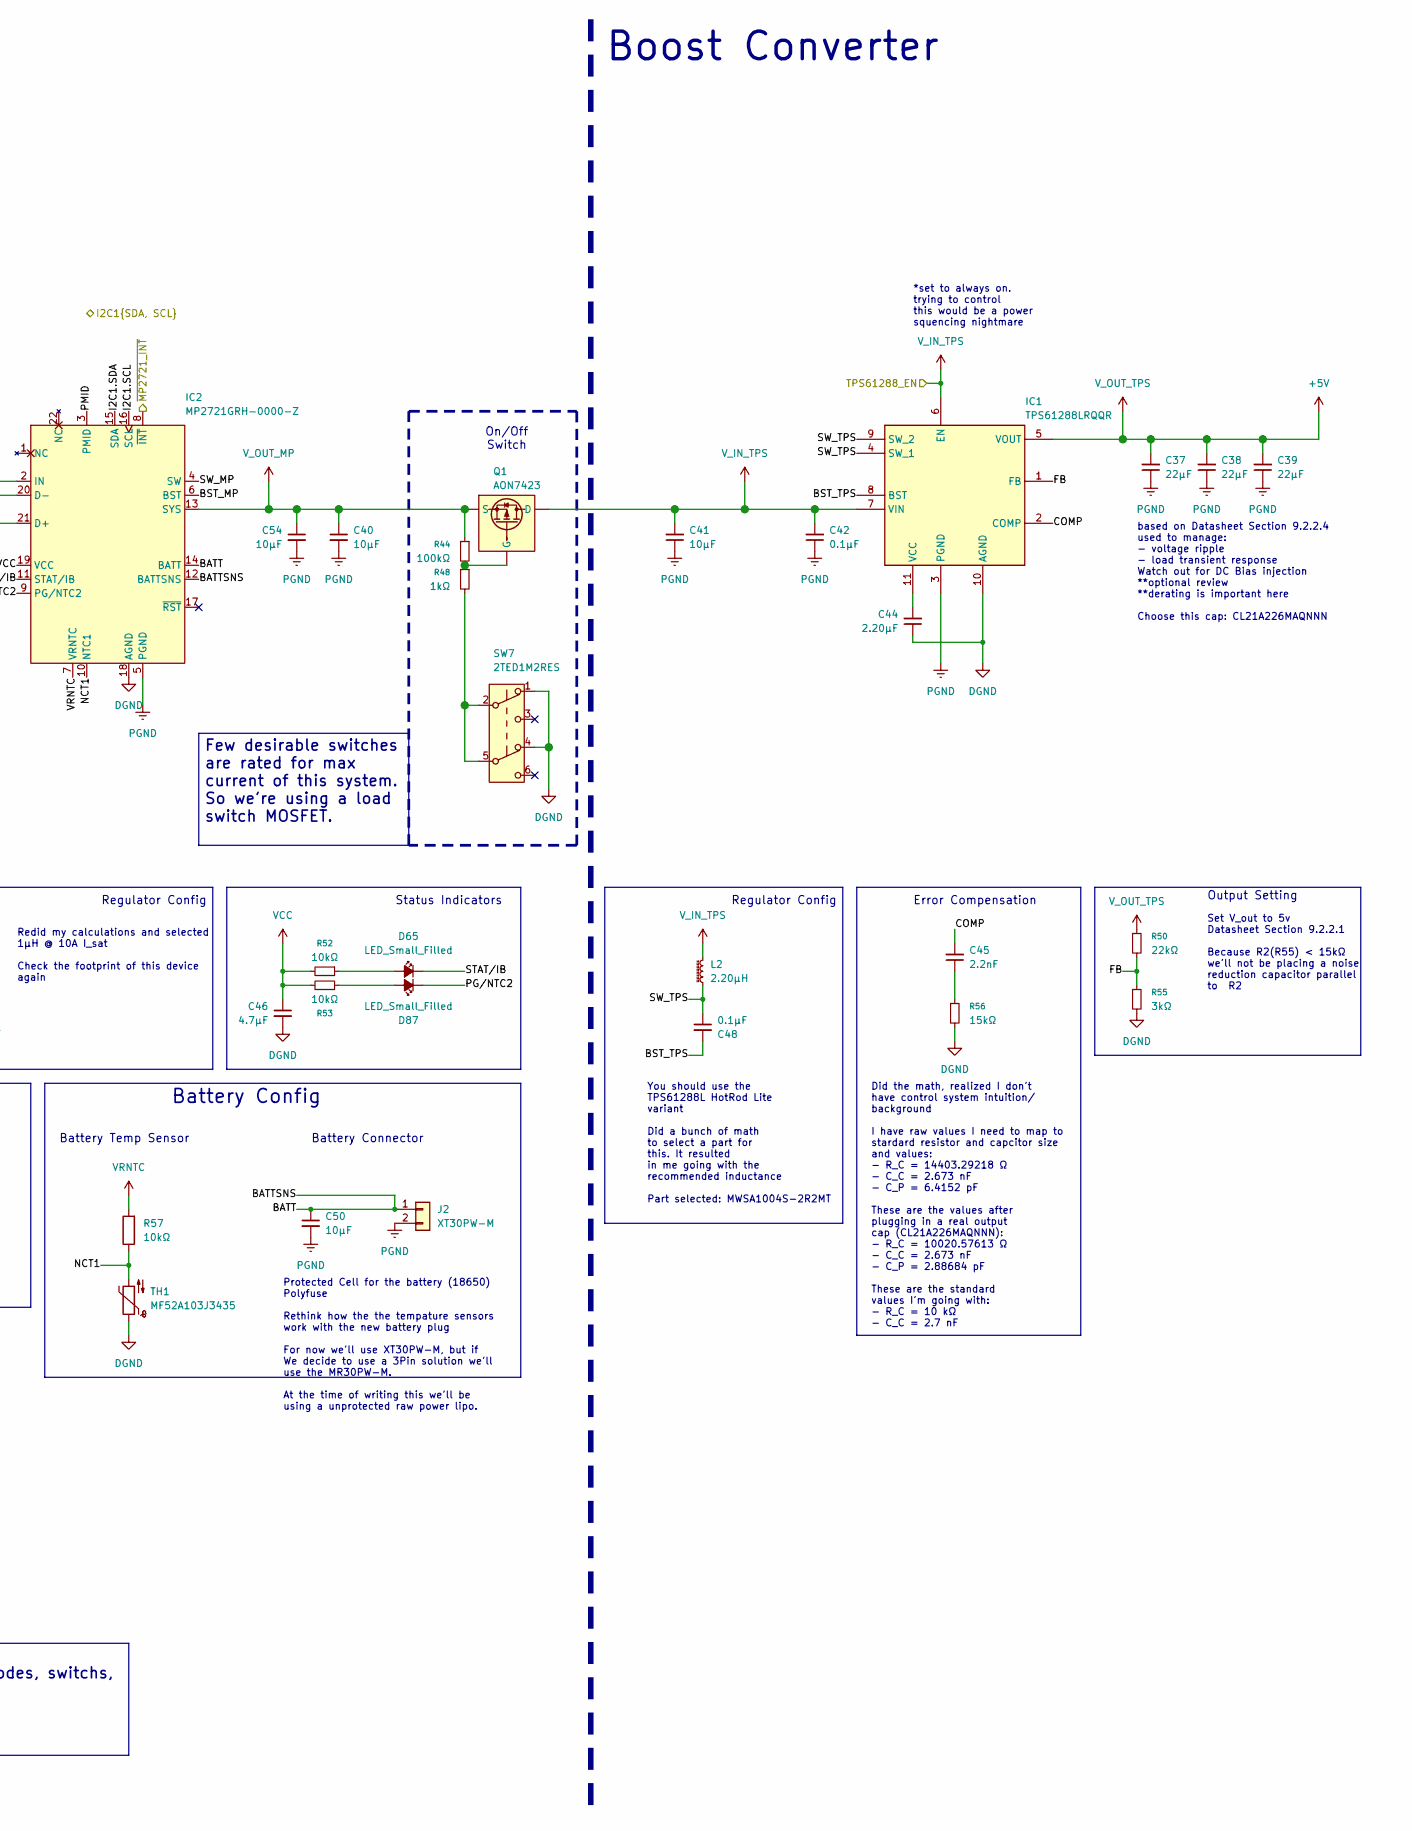
[picture p31: schematic power.kicad_sch, part in row 1, column 2]

Parts:
C37, C38, C39: 22μF; C_0805_2012Metric
C40, C41, C49, C50, C54: 10μF; C_0805_2012Metric
C42, C48: 0.1μF; C_0402_1005Metric
C43: 1μF; C_0402_1005Metric
C44: 2.20μF; C_0805_2012Metric
C45: 2.2nF; C_0805_2012Metric
C46: 4.7μF; C_0805_2012Metric
C47: 22nF; C_1206_3216Metric
D64: USBLC6-2SC6; SOT95P280X145-6N; Manufacturer_Part_Number USBLC6-2SC6; Mouser Part Number 511-USBLC6-2SC6
D65, D87: LED_Small_Filled
D88, D89: 3.6V; D_SOD-123
FL1: EXC14CE900U; Manufacturer_Part_Number EXC14CE900U
IC1: TPS61288LRQQR; PTPS61288RQQR; Manufacturer_Part_Number TPS61288LRQQR; Mouser Part Number 595-TPS61288LRQQR
IC2: MP2721GRH-0000-Z
J1: Female USB-C USB2.0; USB_C_Receptacle_GCT_USB4085
J2: XT30PW-M; AMASS_XT30PW-M_1x02_P2.50mm_Horizontal
JP5, JP6: Jumper_2_Small_Open; PinHeader_1x02_P2.54mm_Vertical
L1: 1μH
L2: 2.20μH; L_Sunlord_MWSA1005S
Q1: AON7423
R44: 100kΩ; R_1206_3216Metric
R48: 1kΩ; R_1206_3216Metric
R49, R51: 5.1kΩ ≤1%; R_0805_2012Metric
R50: 22kΩ; R_0805_2012Metric
R52, R53, R57: 10kΩ; R_0805_2012Metric
R55: 3kΩ; R_0805_2012Metric
R56: 15kΩ; R_0805_2012Metric
R60, R61: 10kΩ ≤1%; R_0805_2012Metric
SW7: 2TED1M2RES
TH1: MF52A103J3435

Connections:
+5V: C37.2, C38.2, C39.2, IC1.5 (VOUT), R50.1
BATT: C50.1, IC2.12 (BATTSNS), IC2.14 (BATT), J2.1
BST_MP: C47.2, IC2.6 (BST)
BST_TPS: C48.2, IC1.8 (BST)
CC1: J1.A5 (CC1), JP5.1 (A), R51.1, R60.1
CC2: J1.B5 (CC2), JP6.1 (A), R49.1, R61.1
COMP: C45.2, IC1.2 (COMP)
DGND: C37.1, C38.1, C39.1, C40.2, C41.1, C42.1, C43.2, C44.1, C46.2, C49.2, C50.2, C54.2, D64.2 (GND), D88.2 (A), D89.2 (A), IC1.3 (PGND), IC1.10 (AGND), IC2.5 (PGND), IC2.18 (AGND), J1.A1 (GND), J1.A12 (GND), J1.B1 (GND), J1.B12 (GND), J1.SH (SHIELD), J2.2, R49.2, R51.2, R55.2, R56.2, SW7.1 (A), SW7.4 (A), TH1.1
FB: IC1.1 (FB), R50.2, R55.1
I2C1.SCL: IC2.16 (SCL)
I2C1.SDA: IC2.15 (SDA)
NCT1: IC2.10 (NTC1), R57.1, TH1.2
unnamed: C44.2, IC1.11 (VCC)
unnamed: C45.1, R56.1
unnamed: D64.1 (I/O1), J1.A7 (D-), J1.B7 (D-)
unnamed: D64.3 (I/O2), J1.A6 (D+), J1.B6 (D+)
unnamed: D64.4 (I/O2), FL1.1
unnamed: D64.6 (I/O1), FL1.2
unnamed: D65.2 (A), R52.1
unnamed: D87.2 (A), R53.1
unnamed: Q1.4 (G), R44.2, R48.1
unnamed: R48.2, SW7.2 (B), SW7.5 (B)
PG/NTC2: D87.1 (K), IC2.9 (PG/NTC2)
PMID: C49.1, IC2.3 (PMID)
STAT/IB: D65.1 (K), IC2.11 (STAT/IB)
SW_MP: C47.1, IC2.4 (SW), L1.2
SW_TPS: C48.1, IC1.4 (SW_1), IC1.9 (SW_2), L2.1
USB.CC1: D88.1 (K), JP5.2 (B), R60.2
USB.CC2: D89.1 (K), JP6.2 (B), R61.2
USB.D+: FL1.4, IC2.21 (D+)
USB.D-: FL1.3, IC2.20 (D-)
VCC: C46.1, IC2.19 (VCC), R52.2, R53.2
VRNTC: IC2.7 (VRNTC), R57.2
V_BUS: C43.1, D64.5 (VBUS), IC2.2 (IN), J1.A4 (VBUS), J1.A9 (VBUS), J1.B4 (VBUS), J1.B9 (VBUS)
V_IN_TPS: C41.2, C42.2, IC1.6 (EN), IC1.7 (VIN), L2.2, Q1.5 (D), Q1.6 (D), Q1.7 (D), Q1.8 (D), Q1.9 (D)
V_OUT_MP: C40.1, C54.1, IC2.13 (SYS), L1.1, Q1.1 (S), Q1.2 (S), Q1.3 (S), R44.1
~MP2721_INT: IC2.8 (~INT)

Notes on the sheet:
Battery Temp Sensor
based on Datasheet Section 9.2.2.4 used to manage: - voltage ripple - load transient response Watch out for DC Bias injection **optional review **derating is important here Choose this cap: CL21A226MAQNNN
On/Off Switch
This cap needs to be rated for +4A, X7R or X5R of current based on the page 40 of the datasheet. I caculated a max current ripple of about 1.3A
Error Compensation
Output Setting
This circuit is designed to provide the option to manually insure highest charging current possible, by reading the USB CC pins voltage I'm uncertain of the necessity of the 10kΩ resistors so I've made them optional.
Battery Connector
Ground Config
Data Line EMI Filter
USB Configuration channel Negotiation
Set V_out to 5v Datasheet Section 9.2.2.1 Because R2(R55) < 15kΩ we'll not be placing a noise reduction capacitor parallel to R2
Charger
Regulator Config
You should use the TPS61288L HotRod Lite variant Did a bunch of math to select a part for this. It resulted in me going with the recommended inductance Part selected: MWSA1004S-2R2MT
Redid my calculations and selected 1μH @ 10A I_sat Check the footprint of this device again
USB-C 2.0
Battery Config
Over Voltage Protection
*set to always on. trying to control this would be a power squencing nightmare
Did the math, realized I don't have control system intuition/ background I have raw values I need to map to stardard resistor and capcitor size and values: - R_C = 14403.29218 Ω - C_C = 2.673 nF - C_P = 6.4152 pF These are the values after plugging in a real output cap (CL21A226MAQNNN): - R_C = 100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
Status Indicators
The resistors provide over current protection, while the zener diodes provide over voltage protection. 3.6V rating is verified by the nrf52480 I/O Pin Voltage spec. Verify Pin Current rating
Boost Converter
PMID Decoupler
Data Line ESD Protection
Protected Cell for the battery (18650) Polyfuse Rethink how the the tempature sensors work with the new battery plug For now we'll use XT30PW-M, but if We decide to use a 3Pin solution we'll use the MR30PW-M. At the time of writing this we'll be using a unprotected raw power lipo.
Do I have enough protect on the USB contector? Do I still need to add resistors or pull up these lines? Have I properly set up the charger and regulator correctily? why can charge current be higher than input current in battery charger Zener Diodes vs Schottky Diode for pin protection
Few desirable switches are rated for max current of this system. So we're using a load switch MOSFET.
Power Ratings per Critical Line USB-C plug → Charger IC input: - max 5V @ 3A - must be configured USB-C plug → Charger IC output: - Worst case output current draw 6A - Max output current 5A - Voltage range 3.125V ↔ 3.913V default 3.7V Battery → Charger IC output: - Worst case discharge current draw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
Selection of passives: resistors, capcitors, inductors, diodes, switchs, LEDs, usb port Consider BQ25640 & BQ25895
