Dreamy-Jy/slack/hardware/v1-electronics/switch_matrix.kicad_sch

## KiCad design hardware/v1-electronics/switch_matrix.kicad_sch (2026-08-18)

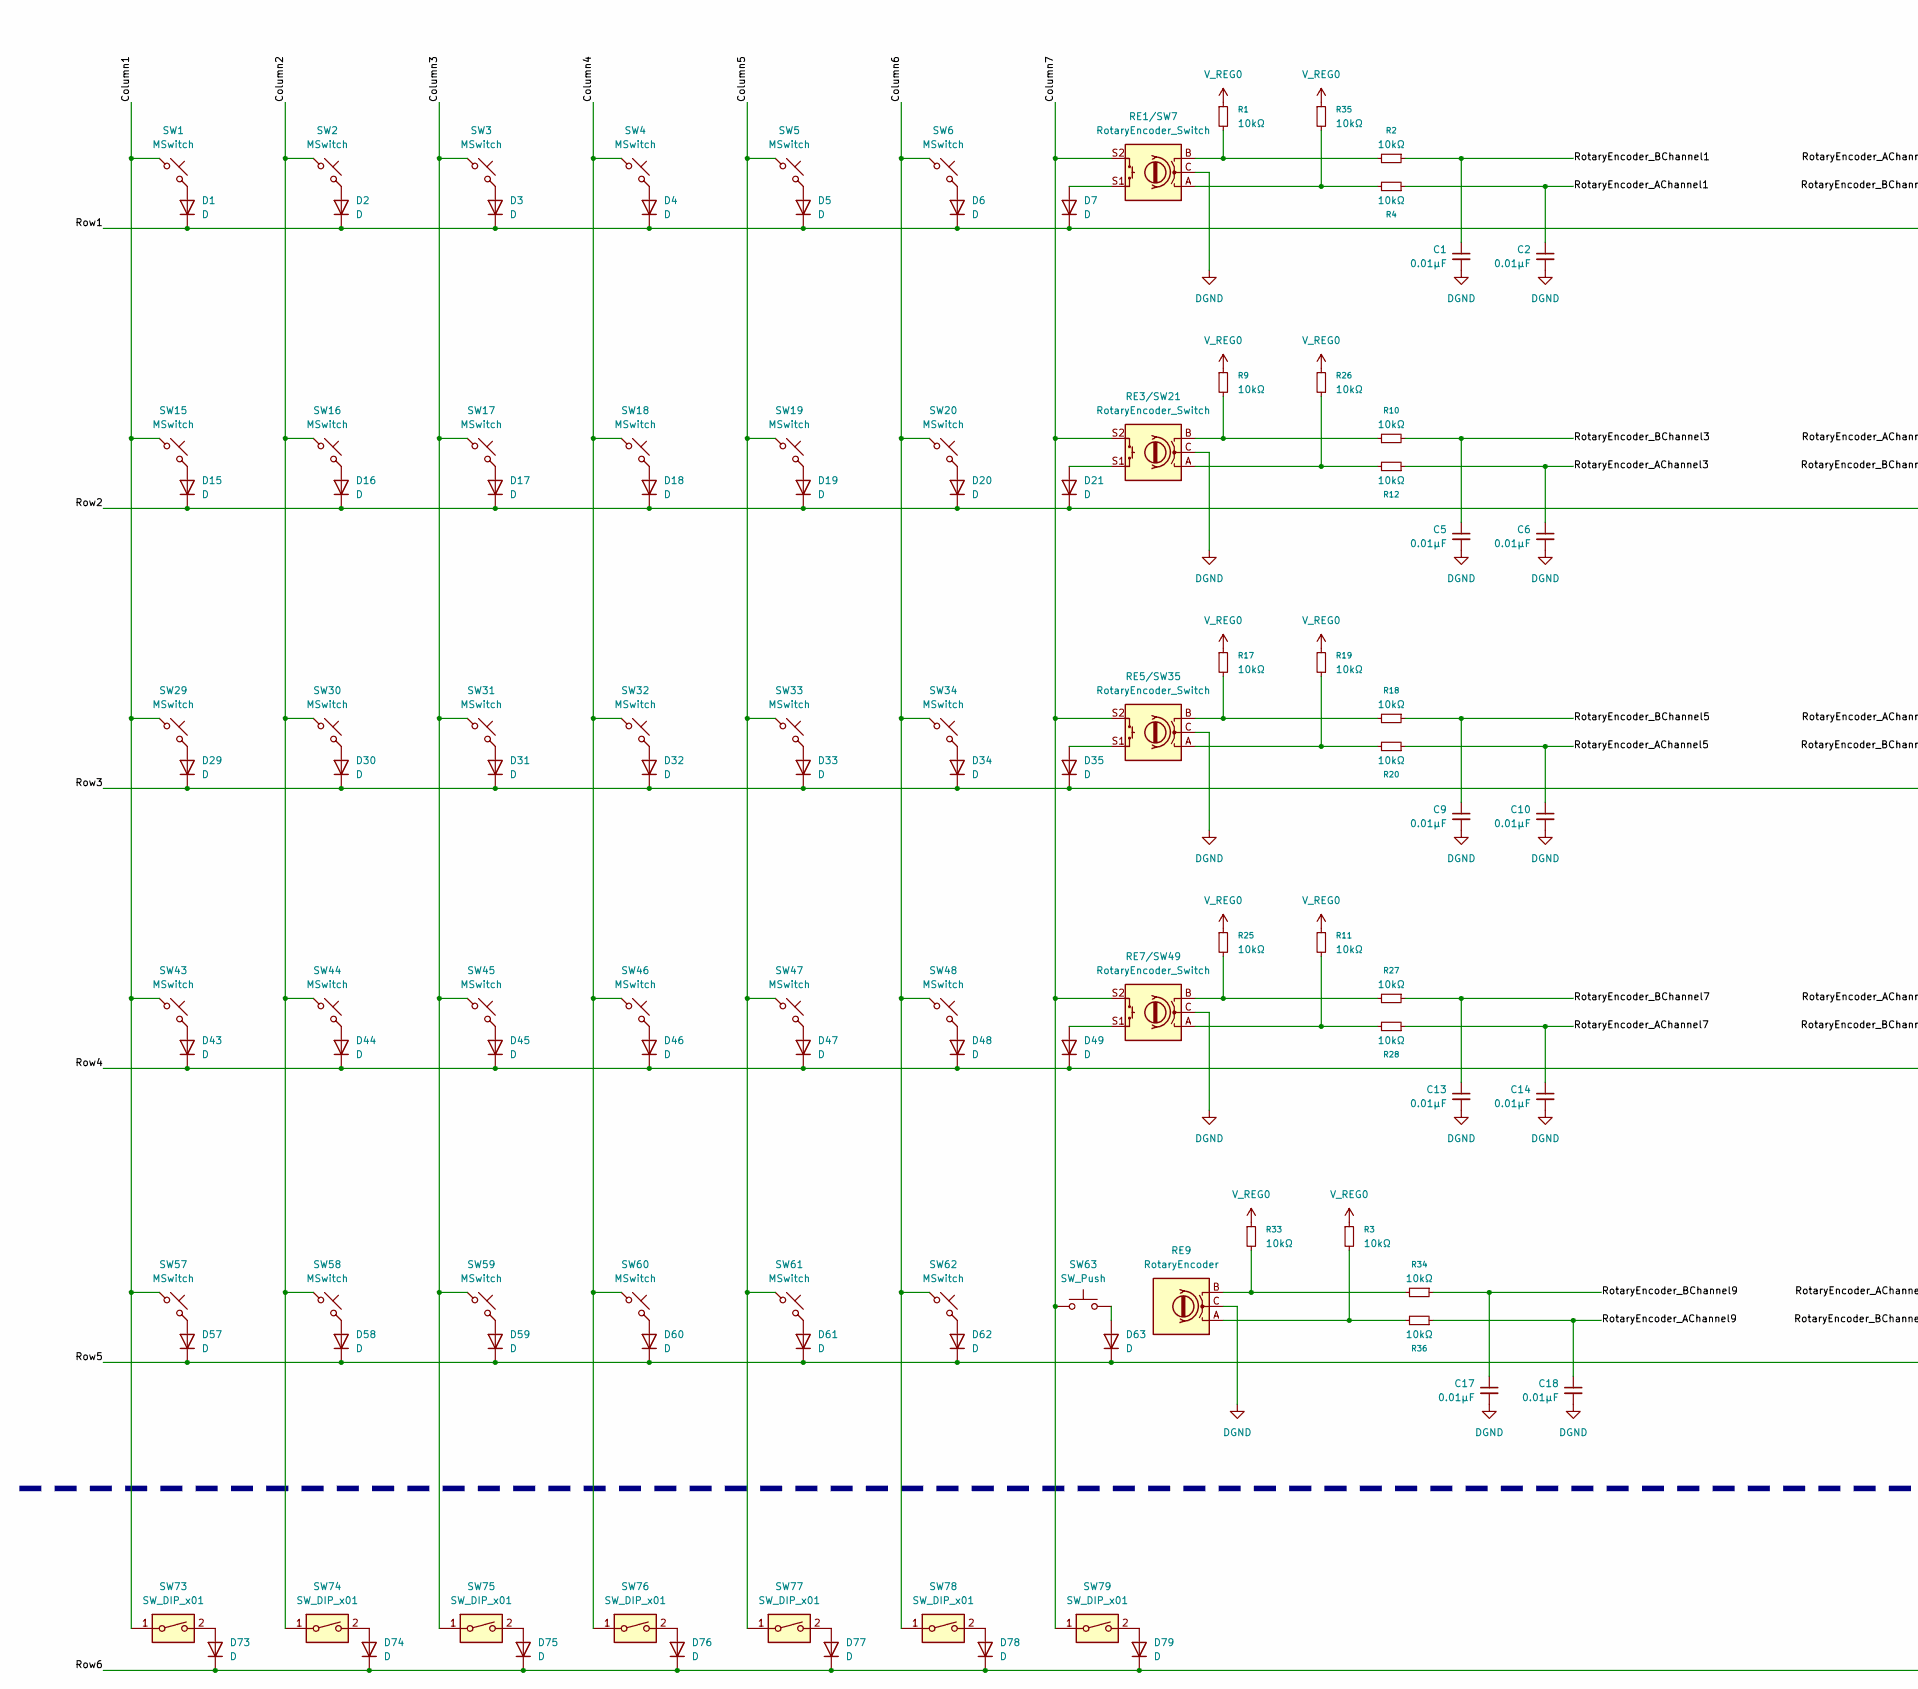
[picture p32: schematic switch_matrix.kicad_sch, part in row 1, column 1]

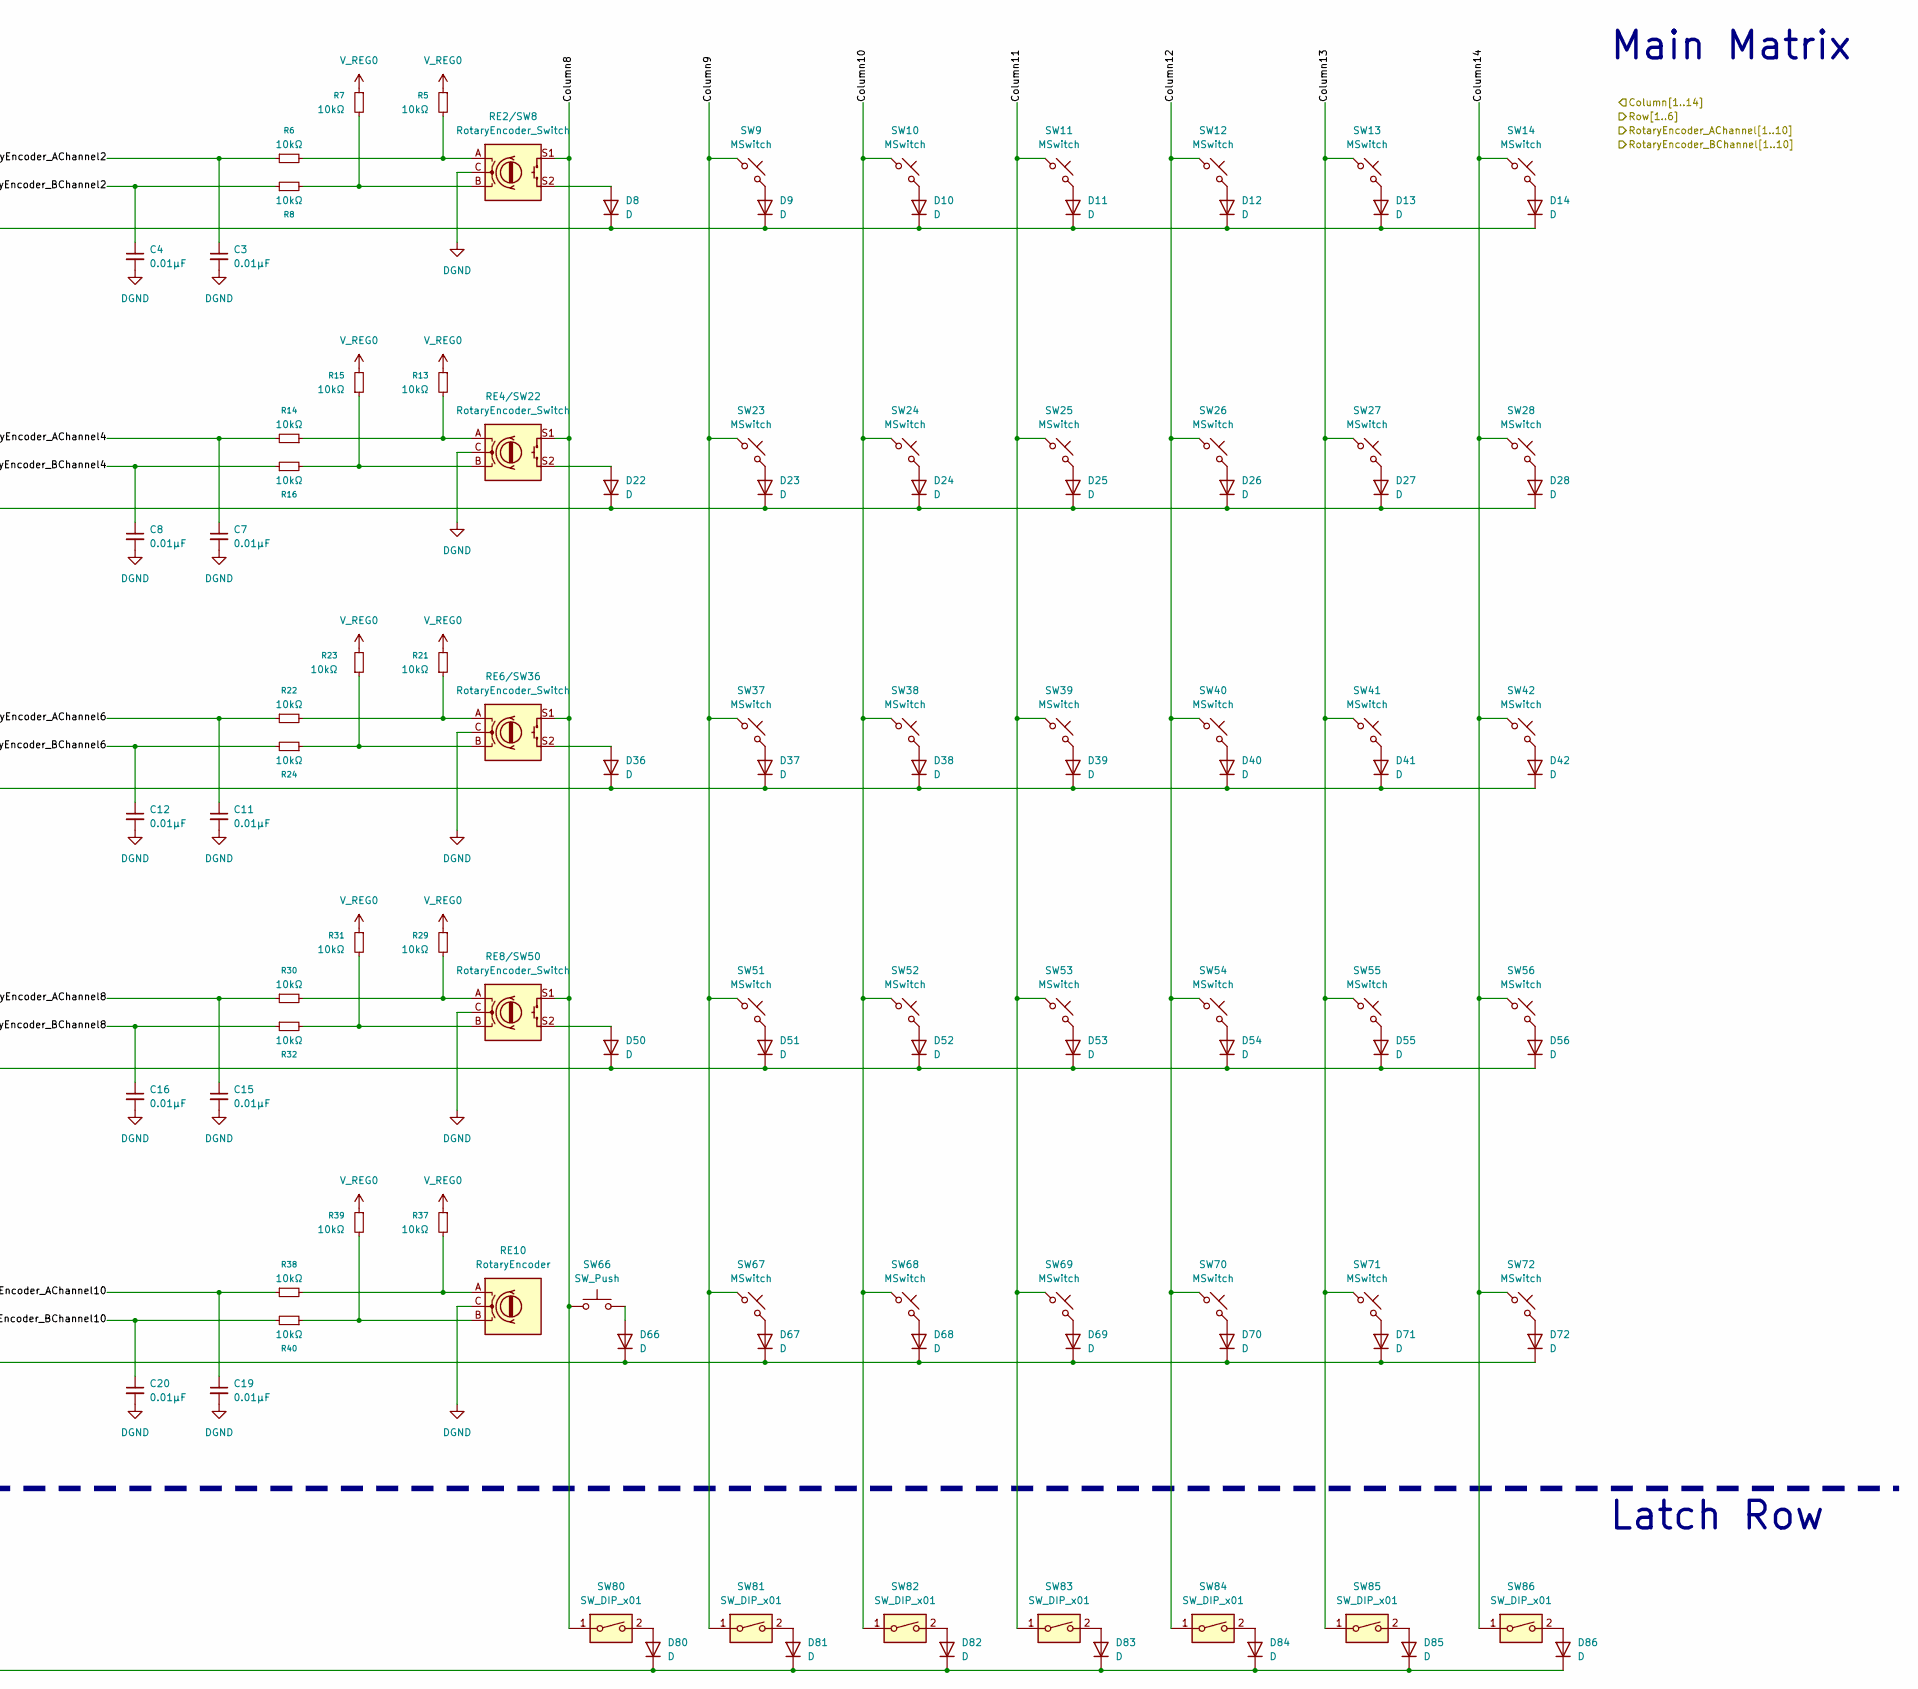
[picture p33: schematic switch_matrix.kicad_sch, part in row 1, column 2]

Parts:
C1, C2, C3, C4, C5, C6, C7, C8, C9, C10, C11, C12, C13, C14, C15, C16, C17, C18, C19, C20: 0.01μF; C_0402_1005Metric
D1, D2, D3, D4, D5, D6, D7, D8, D9, D10, D11, D12, D13, D14, D15, D16, D17, D18, D19, D20, D21, D22, D23, D24, D25, D26, D27, D28, D29, D30, D31, D32, D33, D34, D35, D36, D37, D38, D39, D40, D41, D42, D43, D44, D45, D46, D47, D48, D49, D50, D51, D52, D53, D54, D55, D56, D57, D58, D59, D60, D61, D62, D63, D66, D67, D68, D69, D70, D71, D72, D73, D74, D75, D76, D77, D78, D79, D80, D81, D82, D83, D84, D85, D86: D; D_SOD-523
R1, R2, R3, R4, R5, R6, R7, R8, R9, R10, R11, R12, R13, R14, R15, R16, R17, R18, R19, R20, R21, R22, R23, R24, R25, R26, R27, R28, R29, R30, R31, R32, R33, R34, R35, R36, R37, R38, R39, R40: 10kΩ; R_0805_2012Metric
RE1/SW7, RE2/SW8, RE3/SW21, RE4/SW22, RE5/SW35, RE6/SW36, RE7/SW49, RE8/SW50: RotaryEncoder_Switch; EC09E1524418
RE9, RE10: RotaryEncoder; EC10E1220505
SW1, SW2, SW3, SW4, SW5, SW6, SW9, SW10, SW11, SW12, SW13, SW14, SW15, SW16, SW17, SW18, SW19, SW20, SW23, SW24, SW25, SW26, SW27, SW28, SW29, SW30, SW31, SW32, SW33, SW34, SW37, SW38, SW39, SW40, SW41, SW42, SW43, SW44, SW45, SW46, SW47, SW48, SW51, SW52, SW53, SW54, SW55, SW56, SW57, SW58, SW59, SW60, SW61, SW62, SW67, SW68, SW69, SW70, SW71, SW72: MSwitch; Cherry_ULP_SMD
SW63, SW66: SW_Push; SW_Push_1P1T_XKB_TS-1187A
SW73, SW74, SW75, SW76, SW77, SW78, SW79, SW80, SW81, SW82, SW83, SW84, SW85, SW86: SW_DIP_x01

Connections:
Column1: SW1.1, SW15.1, SW29.1, SW43.1, SW57.1, SW73.1
Column2: SW2.1, SW16.1, SW30.1, SW44.1, SW58.1, SW74.1
Column3: SW3.1, SW17.1, SW31.1, SW45.1, SW59.1, SW75.1
Column4: SW4.1, SW18.1, SW32.1, SW46.1, SW60.1, SW76.1
Column5: SW5.1, SW19.1, SW33.1, SW47.1, SW61.1, SW77.1
Column6: SW6.1, SW20.1, SW34.1, SW48.1, SW62.1, SW78.1
Column7: RE1/SW7.S2, RE3/SW21.S2, RE5/SW35.S2, RE7/SW49.S2, SW63.1, SW79.1
Column8: RE2/SW8.S1, RE4/SW22.S1, RE6/SW36.S1, RE8/SW50.S1, SW66.1, SW80.1
Column9: SW9.1, SW23.1, SW37.1, SW51.1, SW67.1, SW81.1
Column10: SW10.1, SW24.1, SW38.1, SW52.1, SW68.1, SW82.1
Column11: SW11.1, SW25.1, SW39.1, SW53.1, SW69.1, SW83.1
Column12: SW12.1, SW26.1, SW40.1, SW54.1, SW70.1, SW84.1
Column13: SW13.1, SW27.1, SW41.1, SW55.1, SW71.1, SW85.1
Column14: SW14.1, SW28.1, SW42.1, SW56.1, SW72.1, SW86.1
DGND: C1.2, C2.2, C3.2, C4.2, C5.2, C6.2, C7.2, C8.2, C9.2, C10.2, C11.2, C12.2, C13.2, C14.2, C15.2, C16.2, C17.2, C18.2, C19.2, C20.2, RE1/SW7.C, RE2/SW8.C, RE3/SW21.C, RE4/SW22.C, RE5/SW35.C, RE6/SW36.C, RE7/SW49.C, RE8/SW50.C, RE9.C, RE10.C
unnamed: D1.2 (A), SW1.2
unnamed: D2.2 (A), SW2.2
unnamed: D3.2 (A), SW3.2
unnamed: D4.2 (A), SW4.2
unnamed: D5.2 (A), SW5.2
unnamed: D6.2 (A), SW6.2
unnamed: D7.2 (A), RE1/SW7.S1
unnamed: D8.2 (A), RE2/SW8.S2
unnamed: D9.2 (A), SW9.2
unnamed: D10.2 (A), SW10.2
unnamed: D11.2 (A), SW11.2
unnamed: D12.2 (A), SW12.2
unnamed: D13.2 (A), SW13.2
unnamed: D14.2 (A), SW14.2
unnamed: D15.2 (A), SW15.2
unnamed: D16.2 (A), SW16.2
unnamed: D17.2 (A), SW17.2
unnamed: D18.2 (A), SW18.2
unnamed: D19.2 (A), SW19.2
unnamed: D20.2 (A), SW20.2
unnamed: D21.2 (A), RE3/SW21.S1
unnamed: D22.2 (A), RE4/SW22.S2
unnamed: D23.2 (A), SW23.2
unnamed: D24.2 (A), SW24.2
unnamed: D25.2 (A), SW25.2
unnamed: D26.2 (A), SW26.2
unnamed: D27.2 (A), SW27.2
unnamed: D28.2 (A), SW28.2
unnamed: D29.2 (A), SW29.2
unnamed: D30.2 (A), SW30.2
unnamed: D31.2 (A), SW31.2
unnamed: D32.2 (A), SW32.2
unnamed: D33.2 (A), SW33.2
unnamed: D34.2 (A), SW34.2
unnamed: D35.2 (A), RE5/SW35.S1
unnamed: D36.2 (A), RE6/SW36.S2
unnamed: D37.2 (A), SW37.2
unnamed: D38.2 (A), SW38.2
unnamed: D39.2 (A), SW39.2
unnamed: D40.2 (A), SW40.2
unnamed: D41.2 (A), SW41.2
unnamed: D42.2 (A), SW42.2
unnamed: D43.2 (A), SW43.2
unnamed: D44.2 (A), SW44.2
unnamed: D45.2 (A), SW45.2
unnamed: D46.2 (A), SW46.2
unnamed: D47.2 (A), SW47.2
unnamed: D48.2 (A), SW48.2
unnamed: D49.2 (A), RE7/SW49.S1
unnamed: D50.2 (A), RE8/SW50.S2
unnamed: D51.2 (A), SW51.2
unnamed: D52.2 (A), SW52.2
unnamed: D53.2 (A), SW53.2
unnamed: D54.2 (A), SW54.2
unnamed: D55.2 (A), SW55.2
unnamed: D56.2 (A), SW56.2
unnamed: D57.2 (A), SW57.2
unnamed: D58.2 (A), SW58.2
unnamed: D59.2 (A), SW59.2
unnamed: D60.2 (A), SW60.2
unnamed: D61.2 (A), SW61.2
unnamed: D62.2 (A), SW62.2
unnamed: D63.2 (A), SW63.2
unnamed: D66.2 (A), SW66.2
unnamed: D67.2 (A), SW67.2
unnamed: D68.2 (A), SW68.2
unnamed: D69.2 (A), SW69.2
unnamed: D70.2 (A), SW70.2
unnamed: D71.2 (A), SW71.2
unnamed: D72.2 (A), SW72.2
unnamed: D73.2 (A), SW73.2
unnamed: D74.2 (A), SW74.2
unnamed: D75.2 (A), SW75.2
unnamed: D76.2 (A), SW76.2
unnamed: D77.2 (A), SW77.2
unnamed: D78.2 (A), SW78.2
unnamed: D79.2 (A), SW79.2
unnamed: D80.2 (A), SW80.2
unnamed: D81.2 (A), SW81.2
unnamed: D82.2 (A), SW82.2
unnamed: D83.2 (A), SW83.2
unnamed: D84.2 (A), SW84.2
unnamed: D85.2 (A), SW85.2
unnamed: D86.2 (A), SW86.2
unnamed: R1.2, R2.2, RE1/SW7.B
unnamed: R3.2, R36.2, RE9.A
unnamed: R5.2, R6.2, RE2/SW8.A
unnamed: R7.2, R8.2, RE2/SW8.B
unnamed: R9.2, R10.1, RE3/SW21.B
unnamed: R11.2, R28.2, RE7/SW49.A
unnamed: R12.2, R26.1, RE3/SW21.A
unnamed: R13.2, R14.1, RE4/SW22.A
unnamed: R15.1, R16.2, RE4/SW22.B
unnamed: R17.2, R18.2, RE5/SW35.B
unnamed: R19.1, R20.2, RE5/SW35.A
unnamed: R21.1, R22.2, RE6/SW36.A
unnamed: R23.1, R24.1, RE6/SW36.B
unnamed: R25.2, R27.2, RE7/SW49.B
unnamed: R29.2, R30.2, RE8/SW50.A
unnamed: R31.2, R32.2, RE8/SW50.B
unnamed: R33.2, R34.2, RE9.B
unnamed: R4.2, R35.2, RE1/SW7.A
unnamed: R37.2, R38.2, RE10.A
unnamed: R39.2, R40.1, RE10.B
RotaryEncoder_AChannel1: C2.1, R4.1
RotaryEncoder_AChannel2: C3.1, R6.1
RotaryEncoder_AChannel3: C6.1, R12.1
RotaryEncoder_AChannel4: C7.1, R14.2
RotaryEncoder_AChannel5: C10.1, R20.1
RotaryEncoder_AChannel6: C11.1, R22.1
RotaryEncoder_AChannel7: C14.1, R28.1
RotaryEncoder_AChannel8: C15.1, R30.1
RotaryEncoder_AChannel9: C18.1, R36.1
RotaryEncoder_AChannel10: C19.1, R38.1
RotaryEncoder_BChannel1: C1.1, R2.1
RotaryEncoder_BChannel2: C4.1, R8.1
RotaryEncoder_BChannel3: C5.1, R10.2
RotaryEncoder_BChannel4: C8.1, R16.1
RotaryEncoder_BChannel5: C9.1, R18.1
RotaryEncoder_BChannel6: C12.1, R24.2
RotaryEncoder_BChannel7: C13.1, R27.1
RotaryEncoder_BChannel8: C16.1, R32.1
RotaryEncoder_BChannel9: C17.1, R34.1
RotaryEncoder_BChannel10: C20.1, R40.2
Row1: D1.1 (K), D2.1 (K), D3.1 (K), D4.1 (K), D5.1 (K), D6.1 (K), D7.1 (K), D8.1 (K), D9.1 (K), D10.1 (K), D11.1 (K), D12.1 (K), D13.1 (K), D14.1 (K)
Row2: D15.1 (K), D16.1 (K), D17.1 (K), D18.1 (K), D19.1 (K), D20.1 (K), D21.1 (K), D22.1 (K), D23.1 (K), D24.1 (K), D25.1 (K), D26.1 (K), D27.1 (K), D28.1 (K)
Row3: D29.1 (K), D30.1 (K), D31.1 (K), D32.1 (K), D33.1 (K), D34.1 (K), D35.1 (K), D36.1 (K), D37.1 (K), D38.1 (K), D39.1 (K), D40.1 (K), D41.1 (K), D42.1 (K)
Row4: D43.1 (K), D44.1 (K), D45.1 (K), D46.1 (K), D47.1 (K), D48.1 (K), D49.1 (K), D50.1 (K), D51.1 (K), D52.1 (K), D53.1 (K), D54.1 (K), D55.1 (K), D56.1 (K)
Row5: D57.1 (K), D58.1 (K), D59.1 (K), D60.1 (K), D61.1 (K), D62.1 (K), D63.1 (K), D66.1 (K), D67.1 (K), D68.1 (K), D69.1 (K), D70.1 (K), D71.1 (K), D72.1 (K)
Row6: D73.1 (K), D74.1 (K), D75.1 (K), D76.1 (K), D77.1 (K), D78.1 (K), D79.1 (K), D80.1 (K), D81.1 (K), D82.1 (K), D83.1 (K), D84.1 (K), D85.1 (K), D86.1 (K)
V_REG0: R1.1, R3.1, R5.1, R7.1, R9.1, R11.1, R13.1, R15.2, R17.1, R19.2, R21.2, R23.2, R25.1, R26.2, R29.1, R31.1, R33.1, R35.1, R37.1, R39.1

Notes on the sheet:
Latch Row
Main Matrix
