Dreamy-Jy/slack/hardware/v1-simulations/v1-simulations.kicad_sch

## KiCad design hardware/v1-simulations/v1-simulations.kicad_sch (2026-08-18)

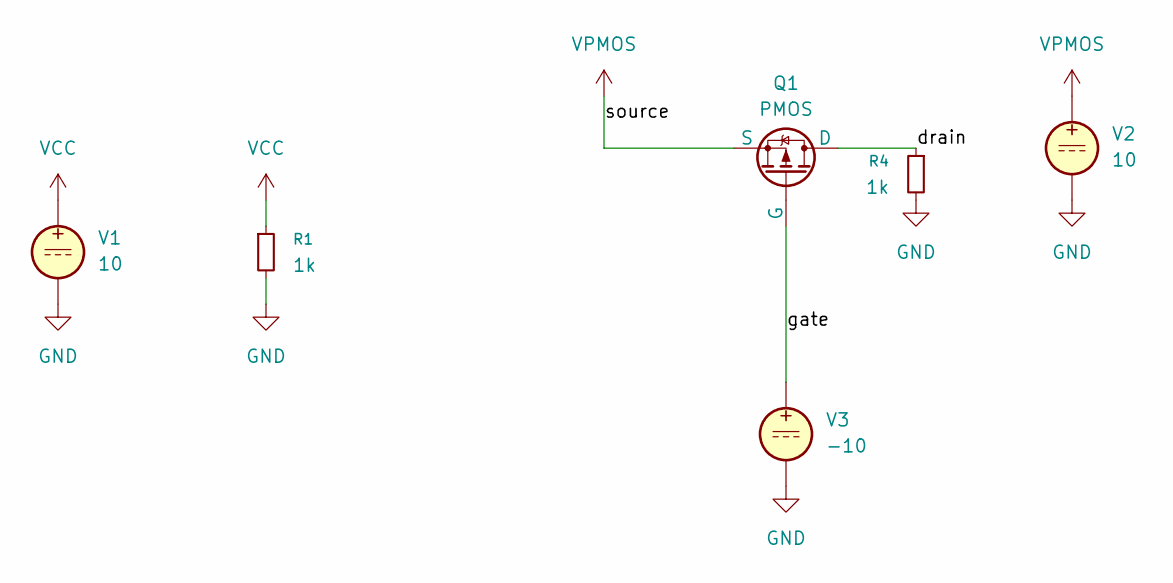
[picture p34: schematic v1-simulations.kicad_sch]

Parts:
Q1: PMOS
R1, R4: 1k
V1, V2: 10
V3: -10

Connections:
GND: R1.2, R4.2, V1.2, V2.2, V3.2
VCC: R1.1, V1.1
VPMOS: Q1.3 (S), V2.1
drain: Q1.1 (D), R4.1
gate: Q1.2 (G), V3.1
